kms254/Mustang-Dash-Test/docs/plans/2026-07-27-003-feat-telltale-driver-and-rail-decoupling-plan.md

---
title: Telltale Driver Chain and Rail Decoupling - Plan
type: feat
date: 2026-07-27
topic: telltale-driver-rail-decoupling
artifact_contract: ce-unified-plan/v1
artifact_readiness: implementation-ready
product_contract_source: ce-plan-bootstrap
execution: code
origin: docs/plans/2026-07-27-002-fix-board3-fab-ready-in-kicad-plan.md
---

# Telltale Driver Chain and Rail Decoupling - Plan

## Goal Capsule

- **Objective:** Replace Board3's Darlington telltale driver with a DMOS array, move the telltales to the PLCC-2 package the automotive industry uses for cluster indicators, re-derive the series resistors from the resulting electrical and photometric reality, and convert the rail bulk capacitance from through-hole to SMD sited at the loads that need it.
- **Continuity:** Units continue the fab-ready plan's numbering at **U10**; requirement IDs continue at **R18**. That plan closed at U9 with the board fab-ready (36 DRC violations, NEW = 0 against the 41-violation import baseline, 0 airwires).
- **Product authority:** Kevin owns the design decisions. This document owns sequencing and the completion bar.
- **Execution profile:** Real design work on a board already declared fab-ready. Every unit must leave it fab-ready.
- **Delivery split (decided 2026-07-27):** U10-U12 are a self-contained, shippable increment. **U13-U14 are GATED** and must not be started until their blocking input arrives.
- **Stop conditions:** Stop and report if DRC rises above the 41-violation import baseline; if a part cannot be sourced with complete LCSC metadata; if the PLCC-2 pitch does not fit; or if a change would alter circuit intent rather than implementation.

---

## Product Contract

### Summary

Board3's eight telltales are driven by a ULN2803A Darlington array whose ~0.8 V saturation drop consumes up to 44% of the available headroom on the high-V<sub>f</sub> colours, holding the blue telltale to 5 mA. Replacing it with a pin-compatible DMOS array drops that to ~5 mV and unlocks the brightness the design was aiming for. Once the driver changes, the series resistors must be re-derived anyway — which makes it the right moment to move the LEDs from 0805 to PLCC-2, the package automotive clusters use because it couples into an icon mask or light pipe instead of producing a hot spot.

Separately, the rail bulk is six 8 mm through-hole cans. Four sit on +5V clustered at the board's east end; two put 440 µF on the 3V3 buck output. They force a through-hole assembly step on an otherwise all-SMT board, and their placement serves only one of three panels.

### Problem Frame

**The driver wastes the headroom the high-V<sub>f</sub> telltales need.** Measured from the parts themselves:

| LED | Colour | V<sub>f</sub> | R now | I now (ULN2803A, ~0.8 V) |
|---|---|---|---|---|
| LED1/2 | green NCD0805G1 | 2.5 V | 390 Ω | 4.4 mA |
| LED3 | white KT-0805W | 2.6 V | 300 Ω | 5.3 mA |
| LED4 | blue XL-2012UBC | 3.2 V | 200 Ω | 5.0 mA |
| LED5 | orange XL-2012UOC | 2.3 V | 470 Ω | 4.0 mA |
| LED6/7 | red NCD0805R1 | 1.6 V | 270 Ω | 9.6 mA |
| LED8 | yellow KT-0805Y | 1.8 V | 300 Ω | 8.0 mA |

On the blue telltale the Darlington takes 0.8 V of the 1.8 V that remains after V<sub>f</sub>. A Darlington's drop also never falls below ~0.7 V and varies with current and temperature, so brightness tracks part spread rather than design intent.

**A second, quieter problem:** the ULN2803A's inputs are current-driven through internal 2.7 kΩ base resistors and are specified against 5 V logic. The H755 drives them at 3.3 V. It works, but with reduced margin — and it is not a condition anyone chose.

**The telltale package is wrong for the job.** 0805 LEDs are small, narrow emitters. Cluster telltales sit behind icon masks or light pipes, which is why PLCC-2 (Osram TOPLED and equivalents) is the industry package: a large emitting surface, ~120° beam, 30-50 mA capability, and an AEC-Q102 inventory that does not exist for these generic 0805 parts.

**The bulk capacitance is in the wrong package and the wrong place.** Six `ERS1EM221F12OT` (220 µF 25 V, THT, LCSC C160162): C1/C12/C13/C14 on +5V at x=260-269, plus C2 and C16 on +3V3. Each FPC already carries a local 10 µF ceramic (C30/C31/C29), and the buck has its input cap (C51). So the 880 µF is additional, is the rail's entire electrolytic budget, and sits at one end — 18 mm from FPC3, 111 mm from FPC2, 210 mm from FPC1. If PWM'd backlight droop justifies it at FPC3, FPC1 and FPC2 are under-provisioned by two orders of magnitude. If it does not, FPC3 does not need it either. Both cannot be true.

### Requirements

**Driver**

- R18. `U10` is a DMOS/MOSFET array whose on-state drop at telltale currents is under 50 mV, replacing the ULN2803A Darlington.
- R19. The replacement is pin-compatible with the existing SOIC-18-300mil land pattern, so the swap changes parts and not layout.
- R20. The replacement's input thresholds are specified for 3.3 V logic.

**Telltales**

- R21. All eight telltales use a PLCC-2 package.
- R22. Parts are AEC-Q102 automotive grade **where that colour is stocked at LCSC**, commercial grade otherwise, with the grade recorded per part.
- R23. The LED row's existing pitch accommodates the larger package without moving neighbouring parts.

**Brightness**

- R24. Series resistors are derived from each chosen LED's V<sub>f</sub> and luminous intensity so the eight telltales are matched in **perceived** brightness, not in current.
- R25. Each telltale runs at the highest current the chosen part and driver allow within their continuous ratings, since global dimming is done in firmware by PWM.

**Bulk capacitance** *(gated — see Scope Boundaries)*

- R26. Rail bulk capacitance is SMD, eliminating the through-hole assembly step.
- R27. Bulk is sited at each FPC's backlight supply pins (17/18 and 19/20), not clustered at one end of the board.
- R28. Total +5V bulk is sized from the panel's actual backlight current, and the resulting USB-C inrush through the U5/U6 ideal-diode ORing is stated.
- R29. The +3V3 bulk is reconciled against the TPS563201's maximum output capacitance for reliable start-up.

**Sourcing and provenance**

- R30. Every part added or changed carries the full metadata set the existing parts carry: `Supplier Part`, `Manufacturer Part`, `Manufacturer`, `JLCPCB Part Class`, `Datasheet`, `LCSC Part Name`.
- R31. Every new R/C/IC carries its value or model number in silkscreen on its own footprint body (standing project rule).
- R32. The board stays fab-ready at every unit boundary: DRC no worse than the 41-violation import baseline, zero airwires, no via inside an SMD pad.

### Scope Boundaries

- **Gated, not deferred: U13 and U14.** The bulk work is fully specified here but must not start until the Riverdi RVT70HSBNWN00 backlight current is known. Riverdi does not publish it in any indexed page; the datasheet PDF or a bench measurement is the unblocking input.
- No 6-layer restack. The reviewer's Top/GND/GND/5V proposal is directionally right about return-path integrity and infeasible on four layers — 2,072 mm of routing currently lives on the three non-top layers and would have to fit on a top layer already carrying 3,308 mm. That is a respin decision with its own plan.
- No inner-plane routing rework. Inner1 carries 934 mm of signal and Inner2 656 mm; that is the board's architecture, not a defect this plan fixes.
- No reopening of U6's walked-back crystal and QSPI work.
- No change to telltale colour assignment or count — eight positions, six colours, as built.
- Firmware is untouched. PWM dimming already exists and is how brightness is trimmed at runtime.

### Dependencies and Assumptions

- KiCad 10.0.5; `kicad-cli` and `pcbnew` reached through `tools/kicad_env.py`.
- Design rules come from `tools/kicad_rules.json`, never the board's `.kicad_pro` (KTD2 of the origin plan). The project file now carries a synced copy of those rules.
- **Update PCB from Schematic is GUI-only and Kevin-run**, with "Re-link footprints to schematic symbols based on their reference designators" ticked. It reads eeschema's cached copy, not the file — restart KiCad after any out-of-editor schematic edit or the sync silently reports no changes.
- Board3 as it stands: 36 DRC violations, NEW = 0 over the 41-violation import baseline, 0 airwires, 145 distinct references, CPL 141 rows, BOM 51 lines all sourced.
- `tools/kicad_fab.py` builds the JLC BOM from the `Supplier Part` field. A part added without it does not warn — it silently drops out of the BOM. This is why R30 is a build dependency rather than a preference.
- Assumed: the LED row's pitch accommodates PLCC-2. **U11 measures this first and stops if it does not.**

### Open Questions

**Blocking for U13-U14 only**

- Riverdi RVT70HSBNWN00 backlight LED current at full brightness, and whether the module's backlight driver takes PWM on its own dim pin. If it does, its input capacitance smooths the 5 V draw and the bulk requirement collapses.
- ~~The TPS563201's maximum output capacitance for reliable soft-start, against the present 440 µF.~~ **Answered 2026-07-28**, from the datasheet, while researching U15 of the origin plan. TI publishes **no absolute maximum** C<sub>out</sub> for this part. What it publishes is a *recommended range*: SLVSD90B Table 7-2's 3.3 V row gives C8+C9 = **20 to 68 µF**, restated in §7.2.2.2 as "Recommended values range from 20 µF to 68 µF". `C48`+`C49` = 44 µF sits mid-window; the 440 µF on `C2`/`C16` is ~6.5× the top of it.

  The binding constraint is not soft-start but **D-CAP2 loop stability, and it is two-sided** — SLVAF11 gives both an upper and a lower limit on C<sub>out</sub>, because crossover must stay above the internal ripple-injection zero for a −20 dB/dec crossing and below f<sub>sw</sub>/3. More bulk lowers crossover, and SLVA905 Table 4 measures phase margin *falling* when bandwidth drops below that zero. So "more capacitance is safer" is false for this topology. The catch: evaluating SLVAF11's limit needs the device's A<sub>cp</sub> and ω<sub>RI</sub> constants, which TI publishes for three other parts and **not** for the TPS563201 — so the computed bound is unavailable and Table 7-2's window is the authority.

  That leaves U13/U14 a better-posed question than "what is the maximum": **how much of the 440 µF the loop actually sees.** The +3V3 rail has no pour on any layer — 514.7 mm of 0.254 mm top-layer trace across 195 segments serving 74 pads — so distant bulk is decoupled from the control loop by real series resistance. `C2` measures 260.98 mm of routed path from `L2` pad 2, roughly 0.5 Ω at 1 oz copper; that is not a capacitor the loop can see. Bulk sited *close* to the buck output would be. U14's relocation to the FPC pins therefore wants a per-site path-length figure rather than a lump total, and it is moving bulk **nearer** the regulator that carries loop risk, not leaving it far away.

  Sources: SLVSD90B (Dec 2015, rev Sept 2024) Table 7-2 and §7.2.2.2; SLVAF11 §3.1 Eq 11 and 15; SLVA905 §2.2 Table 4. Path lengths measured from the board file. This resolves the C<sub>out</sub> half of the U13/U14 gate only — the backlight-current blocker above still stands, so the units stay gated.

**Resolvable inside U11-U12**

- ~~Which of the six colours are stocked at LCSC in AEC-Q102 PLCC-2, and what each one's V<sub>f</sub> and mcd-at-test-current are.~~ **Answered 2026-07-28** — the part set and its figures are KTD13. Two results worth stating apart from the table:

  **No colour is stocked in AEC-Q102 in this package**, so R22's conditional resolves to commercial grade across all eight positions. Caveat on how strong that negative is: LCSC does not expose AEC-Q102 as a filterable attribute — qualification lives in free text or only in the datasheet — so this is a negative from a weak search surface, the same shape as `docs/solutions/developer-experience/search-a-package-by-both-its-jedec-and-metric-names.md`. Enough to proceed on; not enough to call the catalogue exhausted.

  **The white part publishes no luminous intensity at all** — LCSC's `Luminous Intensity` for `C516299` is `-`, with a 6500 K colour temperature in its place. That is a real open input to U12, not a lookup that was skipped.

**New, blocking for U12 only**

- ~~White (`C516299`) has no published mcd, so it cannot be put on the same intensity axis as the other five from catalogue data.~~ **Answered 2026-07-28, by the second of the three listed routes** (the datasheet specifies flux, not intensity — there is no mcd bin table to read). From the manufacturer datasheet (SPEC NO B-17-A-1257, REV A/3, 2019-06-17, via LCSC):

  | CCT row | Φ min | Φ typ | conditions |
  |---|---|---|---|
  | 6500 K *(our 6000–7000 K variant)* | 7.5 lm | 8.5 lm | I<sub>F</sub> = 20 mA, tolerance ±10% |

  Also: V<sub>f</sub> 2.6–3.2 V at 20 mA, viewing angle 120°, Ra ≥ 80, SDCM ≤ 3.

  **Conversion to the row's axis:** a 120° part is Lambertian by definition (half-intensity at 60° *is* the cosine pattern), so I₀ = Φ/π: **typ ≈ 2 700 mcd, min ≈ 2 390 mcd**. Sanity: 8.5 lm ÷ (20 mA × ~3.0 V) ≈ 142 lm/W — right for a modern mid-grade white, so the conversion hides no error. The white is therefore the **brightest** position on the row's axis (green 1 300, orange ~1 800 loose, blue 350, red 270, yellow 210 mcd) — U12's matching target is set by the dim end, and the white takes a large resistor, not a guess. Use the **min** figure for worst-case matching; the ±10% flux tolerance and the Lambertian idealisation are the stated error bars.

---

## Planning Contract

Product Contract authored here (`ce-plan-bootstrap`) from the design review discussion of 2026-07-27; the origin plan supplied board state and the verification bar, not these requirements. **Product Contract preservation:** origin plan unchanged — this is a successor, not an edit.

### Key Technical Decisions

**KTD7. The driver is `TBD62083AFWG` (LCSC C165895, SOIC-18-300mil).** R<sub>DS(on)</sub> 325 mΩ, 8 channels, 2.5-30 V input, 2503 in stock. At 15 mA per channel the drop is **4.9 mV** against the Darlington's ~800 mV, and its input thresholds are specified for 3 V logic. It is the industry drop-in for the ULN2803A and matches U10's existing `SOIC-18_L11.6-W7.5-H2.7-LS10.3-P1.27` land pattern, so the board change is a part swap. `C108880` is the same die in SOP-18-300mil at roughly half the price if that land pattern turns out to suit better.

**KTD8. The LED package changes before the resistors are calculated, not after.** Both inputs to the resistor derivation — V<sub>f</sub> and mcd — are properties of the LED. Calculating resistors for the 0805s and then swapping the package throws the calculation away. U11 therefore precedes U12, and U12 consumes U11's chosen parts.

**KTD9 [superseded 2026-07-29 — the perceived-brightness principle survives as the calibration table's seed math; the resistor mechanism died with U12's supersession, see plan 2026-07-28-001 KTD17]. Resistors are derived for equal PERCEIVED brightness, not equal current.** The eye's photopic response peaks near 555 nm, so equal current across six colours produces visibly unequal telltales. The derivation is: for each part, read luminous intensity at its test current, pick a target perceived output achievable by every colour within its continuous rating, then solve `R = (5 − V_f − I·R_DS(on)) / I` per colour. Equal-current is the starting point and the wrong answer.

**KTD10. Mixed-grade BOM, tracked per part.** AEC-Q102 where a colour is stocked in it, commercial otherwise. This maximises availability without silently downgrading the whole row, and the grade is recorded per part so a future production run can close the gaps deliberately.

**KTD11. Every unit ends fab-ready, and "DRC clean" is not the bar.** U6's regression is the standing lesson: six vias buried inside the flash's SMD pads passed DRC and passed a length/via/layer measurement, because via-in-pad is neither. Each unit's verification therefore includes the pad audit and a `kicad_measure --against` diff proving only the intended nets moved.

**KTD12. The schematic-to-board loop has a human in it.** Each unit that changes parts follows: agent edits the schematic as text → **Kevin runs Update PCB from Schematic in the GUI** → agent places, routes, verifies. This is not a limitation to engineer around; it is the one step with no CLI equivalent. Units are shaped so each needs exactly one crossing of it.

**KTD13. The telltale row is HONGLITRONIC HL-A at 20 mA and 120°, except orange, which has no HL-A part and breaks the series deliberately.** Selected and verified against LCSC on 2026-07-28; all six are `SMD3528-2P`, all Extended library, all commercial grade (see Open Questions on AEC-Q102).

| Position | Colour | LCSC | MPN | V<sub>f</sub> | mcd @ 20 mA | Lens | Stock |
|---|---|---|---|---|---|---|---|
| LED1, LED2 | emerald green | `C516142` | HL-A-3528U51GC-S1-13HL | 3.4 V | 1300 | water clear | 65,431 |
| LED3 | white 6500 K | `C516299` | HL-A-3528H343W-S1-13HL-HR3 | 3.2 V | ≈2 700 (from 8.5 lm typ, Lambertian; min ≈2 390 — see Open Questions) | frosted yellow | 100,134 |
| LED4 | blue | `C516143` | HL-A-3528H203BC-S1-13HL | 3.4 V | 350 | water clear | 21,061 |
| LED5 | orange | `C5246349` | HVO-3528CPXA | 2.2 V | 1800 | white lens | 2,000 |
| LED6, LED7 | red | `C516141` | HL-A-3528S35FC-S1-13HL | 2.4 V | 270 | water clear | 26,687 |
| LED8 | yellow | `C516140` | HL-A-3528S31YC-S1-13HL | 2.4 V | 210 | water clear | 24,142 |

Holding one vendor series at one test current and one beam angle is what makes these mcd figures comparable at all — `docs/solutions/conventions/luminous-intensity-is-not-comparable-across-parts.md` is the reasoning, and it is load-bearing for U12.

**Orange is the exception and it is not a slip.** There is no HL-A 3528 orange at LCSC, so the choices were HVO-3528CPXA (orange, 1.8 cd, white lens) or HVA-3528CPXA (`C5246348`, amber, 560 mcd/1.8 cd). HVO wins on being the colour the board already calls for rather than a substitution, and on already carrying a vendor CAD model. The costs are real and should be visible rather than discovered later: it is a different series, so its figure is only loosely comparable to the other five; it has a **white diffusing lens** where the rest are water clear, which changes apparent colour and on-axis intensity independently of the number; stock is 2,000 against 21k-100k for the HL-A parts, the thinnest line in the row; and at $0.12 it is roughly 6× the others. If the orange telltale later needs re-sourcing, this is the position to expect it at.

**The blue is why a 3D model was hand-derived.** Everlight's `67-21/BHC-FQ1R2F/2T` (`C264601`) was the blue with a ready CAD model, quoted `72~180 mcd` — a 2.5× bin spread inside one part number, wider than the matching precision U12 is chasing. `C516143`'s single 350 mcd figure is worth more than a free STEP file, so the model was derived by recolouring a sibling HL-A body and the row stayed in series. `C264601`, `HVT-3528CPX` (`C5246350`, green) and `HVY-3528CPX` (`C2843418`, yellow) are the candidates this decision retired.

### High-Level Technical Design

```mermaid
flowchart TB
  subgraph SHIP["Shippable increment"]
    U10["U10 Driver swap<br/>ULN2803A -> TBD62083AFWG"]
    U11["U11 Telltales to PLCC-2<br/>8 positions, 6 colours"]
    U12["U12 Resistors re-derived<br/>perceived-brightness matched"]
  end
  subgraph GATED["GATED on the backlight spec"]
    U13["U13 Bulk THT -> SMD"]
    U14["U14 Bulk relocated to<br/>FPC pins 17/18 + 19/20"]
  end
  BLOCK{{"Riverdi backlight current<br/>+ TPS563201 max Cout"}}

  U10 --> U12
  U11 --> U12
  U12 --> DONE["Fab package regenerated"]
  BLOCK -.unblocks.-> U13
  U13 --> U14
  U14 --> DONE
```

The dependency that matters is U10 **and** U11 both feeding U12: the resistor value for each telltale depends on the driver's drop and on that LED's V<sub>f</sub> and mcd. U10 and U11 are independent of each other and can be authored in either order, but both must land before U12's arithmetic is real.

Per-unit, the loop is the same shape:

```mermaid
sequenceDiagram
  participant A as Agent
  participant K as Kevin (GUI)
  participant B as Board
  A->>A: edit .kicad_sch as text, verify by netlist export
  A->>K: hand off for Update PCB from Schematic
  K->>B: sync (re-link footprints ticked)
  A->>B: place, route, refill under real rules
  A->>A: DRC delta, airwires, pad audit, net diff
```

---

## Implementation Units

| U-ID | Title | Key files | Depends on |
|---|---|---|---|
| U10 | Driver swap to TBD62083AFWG | `kicad/board3/*.kicad_sch`, `*.kicad_pcb` | — |
| U11 | Telltales to PLCC-2 | `kicad/board3/*.kicad_sch`, `*.pretty/`, `*.kicad_pcb` | — |
| U12 | Resistors re-derived | `kicad/board3/*.kicad_sch`, `*.kicad_pcb` | U10, U11 |
| U13 | Bulk THT to SMD **(gated)** | `kicad/board3/*.kicad_sch`, `*.pretty/` | backlight spec |
| U14 | Bulk relocated to FPC pins **(gated)** | `kicad/board3/*.kicad_pcb` | U13 |

### U10. Swap the Darlington array for a DMOS array

**Goal:** Get the ~0.8 V driver drop out of the telltale chain.

**Requirements:** R18, R19, R20, R30, R31.

**Dependencies:** None.

**Files:** `kicad/board3/ProPrj_New Project_2026-07-15_23-14-34_2026-07-27.kicad_sch`, `kicad/board3/ProPrj_New Project_2026-07-15_23-14-34_2026-07-27.kicad_pcb`

**Approach:** Change U10's part from `ULN2803A` (C181731) to `TBD62083AFWG` (C165895) by editing the symbol's properties in place — value, footprint if the land pattern differs, `Supplier Part`, `Manufacturer Part`, `Manufacturer`, `JLCPCB Part Class`, `Datasheet`, `LCSC Part Name`. Confirm before editing that the two parts agree on all 18 pins: inputs 1-8, GND 9, COM 10, outputs 11-18, and that the replacement carries the output clamp diodes to COM that the flyback path relies on. If the existing SOIC-18 land pattern matches, the PCB change is nil and no re-placement is needed.

**Execution note:** Verify the pinout against the datasheet before touching the schematic. A "pin-compatible" part that is not is the failure mode here, and it is silent until assembly.

**Patterns to follow:** The property set on any existing sourced part; `tools/kicad_lcsc.py` documents which field names this project reads.

**Test scenarios:**
- Covers R18. Netlist export shows U10's eight input nets and eight output nets unchanged, node-for-node, against the pre-edit netlist.
- Covers R19. The footprint property is unchanged, or if changed, the new land pattern is verified against the part's datasheet dimensions.
- Covers R30. `python tools/kicad_fab.py kicad/board3/ --out fab/` reports the same "51 sourced, 0 without LCSC or MPN" — the new part appears with its LCSC code, not blank.
- Covers R32. DRC delta is zero and airwires stay at 0.
- ERC delta is zero or fully attributable to the part change.

**Verification:** U10 carries the DMOS part with complete metadata, the netlist is unchanged, and the board is untouched or re-verified.

### U11. Move the telltales to PLCC-2

**Goal:** Put the eight telltales in the package cluster indicators actually use.

**Requirements:** R21, R22, R23, R30, R31.

**Dependencies:** None.

**Files:** `kicad/board3/ProPrj_New Project_2026-07-15_23-14-34_2026-07-27.kicad_sch`, `kicad/board3/ProPrj_New-easyedapro.pretty/`, `kicad/board3/ProPrj_New Project_2026-07-15_23-14-34_2026-07-27.kicad_pcb`

**Approach:** ~~**Measure the LED row pitch first.**~~ **Measured 2026-07-28. R23 passes, and the premise behind it was wrong.**

**The telltales are not a row.** They are two 2×2 clusters at opposite ends of a 250 × 50 mm board, 150 mm apart: LED1/3/5/7 at x = 65/75, LED2/4/6/8 at x = 225/235, all at y = 90 and 95, every part at rot −90. Pitch is **10.000 mm in X, 5.000 mm in Y**, identical in both clusters. Nothing in this unit depends on the row reading, but the plan asserted it and the board does not support it — later work should not inherit it.

Clearance is computed per adjacent pair as `pitch − halfA − halfB` from the authored courtyards and the real placement, because the six parts have different land patterns and the tightest pair is not the average one. The Y axis (5.000 mm pitch, parts at rot −90 so each package's long axis runs vertically) is the only one that is close:

| Pair | Colours | Σ half-courtyard | Gap |
|---|---|---|---|
| LED4 ↔ LED6 | blue + red | 4.750 mm | **0.250 mm** |
| LED3 ↔ LED7 | white + red | 4.543 mm | 0.457 mm |
| LED1 ↔ LED5 | green + orange | 4.200 mm | 0.800 mm |
| LED2 ↔ LED8 | green + yellow | 4.150 mm | 0.850 mm |
| all X pairs | — | 3.300 mm | 6.700 mm |

**R23 is satisfied — every gap is positive and no neighbour moves** — but the worst case falls from **1.300 mm today to 0.250 mm**, a 5× reduction concentrated on one pair. The blue is the driver: its land pattern is the widest of the six (5.100 mm courtyard against 4.100-4.685 for the rest). Treat y = 90-95 as spoken for from here on, and expect `courtyards_overlap` to be sensitive to any future nudge in that band.

These are **predicted** figures — the board still carries 0805 land patterns until the GUI sync, so they are computed from placement plus the authored courtyards, not read back from a synced board. Confirming them is part of the board half.

**The imported footprints have no courtyard at all, and that has to be fixed here.** All nine `JLCImport.pretty/` footprints carry only `F.Cu`, `F.SilkS` and `F.Fab` — JLCImport does not emit `F.CrtYd`. This is not cosmetic:

- `courtyards_overlap` is **25 of the board's 36 DRC violations**. Swapping in eight courtyard-less footprints makes that count *fall*, and not because the board improved — eight parts would simply stop being checked. A DRC delta computed across that swap would read as an improvement while measuring less than it did before. This is `docs/solutions/conventions/a-gate-that-cannot-pass-gets-waved-through.md` exactly.
- R23 is enforced by courtyard clearance. Without a courtyard there is nothing for DRC to enforce, and the 0.600 mm above is a number no tool will ever re-check.

So U11 authors `F.CrtYd` on the six footprints it uses, sized IPC-7351-style at 0.25 mm around the true occupied extent (pads dominate the long axis at ±1.95 mm, the silk body dominates the short axis at ±1.40 mm → 4.40 × 3.30 mm for the representative part; compute per part rather than assuming, since body length varies 3.2-3.5 mm across the set). The 0.600 mm figure above is the number this makes enforceable.

Part selection is closed — **KTD13 is the answer**, verified against LCSC on 2026-07-28, and its six parts are already imported into `JLCImport.kicad_sym` / `JLCImport.pretty/` with 3D models. What remains is applying them: swap each of LED1-8's `lib_id`, `Value`, `Footprint` and the full supplier field set, then hand off for the board sync.

**This unit splits at the GUI boundary, and the split is the point.** 0805 → PLCC-2 is a *footprint* change, which is the case `kicad/README.md` and KTD12 say genuinely needs Update PCB from Schematic — unlike U10's pure part swap onto an identical land pattern, which `fp.SetValue()` closed with no sync. So:

- **Schematic half (agent, autonomous):** symbol swap, metadata, retired-import cleanup, pitch measurement, and every check that reads the schematic — netlist, ERC, `kicad_lcsc.py check` and `duplicates`.
- **Board half (Kevin, GUI, then agent):** Update PCB from Schematic with re-link-by-reference ticked and KiCad restarted first, then placement, DRC delta, pad audit, renders and fab regeneration.

The intermediate state is a repo where the schematic specifies 3528 and the board still carries 0805 land patterns. That is legible and intentional, but it is **not fab-ready** — do not regenerate `fab/` from it, and say so on any PR that lands the schematic half alone.

**The symbol swap is polarity-unsafe and is not a field edit. Discovered 2026-07-28, and it stops the swap.**

Both sides of this swap use inconsistent anode/cathode conventions, so a symbol-for-symbol replacement silently reverse-biases some telltales.

The board today, read from pad nets:

| Anode on pad 1 | Anode on pad 2 |
|---|---|
| LED1, LED2, LED3, LED8 | LED4, LED5, LED6, LED7 |

This is not a defect — it is the faithful image of six source symbols that disagree with each other (`FC-2012UGK-520D5` and `whiteLEDSMD` put pin 1 = A at x +5.08; `XL-2012UBC`, `XL-2012UOC` and `FC-2012HRK-620D` put pin 1 = K/− at x −5.08; `17-21SUYC/TR8` puts pin 1 = + at x +5.08). The replacements disagree too, and differently: `HL-A-3528U51GC` is pin 1 = C at x −5.08, `HVO-3528CPXA` is pin 1 = K at x −5.08, but `HL-A-3528S35FC` is pin 1 = K at **x +5.08** — mirrored against its own siblings.

Two independent hazards, only one of which any gate catches:

- **Geometric.** Schematic wires attach at coordinates. When pin 1 moves from x +5.08 to x −5.08, the wire that met pin 1 now meets pin 2 and the nets swap. The netlist diff catches this.
- **Electrical.** Anode and cathode change pin number without changing net topology. The netlist still shows two nodes on the right nets, **ERC passes, DRC passes, the BOM is correct, and the telltale is fitted backwards.** Behind a low-side DMOS array a reversed LED simply never lights. Nothing in the verification contract sees it — this is KTD11's lesson in a new place.

So each position needs its anode pin landed on `/+5V` and its cathode on `/TT*_LED_K` individually, by choosing the symbol instance's mirror/rotation per LED — not by rewriting `lib_id` and the property block.

**Resolved 2026-07-28 (Kevin): normalise, and the geometry allows it.**

**KTD14. Every telltale is wired pad 1 = cathode, pad 2 = anode.** Three things make this cheap rather than the re-routing exercise it first looked like:

- **All six replacements already agree electrically.** Pin/pad 1 is the cathode on every one — `C`, `K` or `−` depending on how the vendor labelled it. The red `HL-A-3528S35FC` is *geometrically* mirrored (pad 1 at local x +1.35 where its five siblings put it at −1.35), but it is internally self-consistent, so it needs no special handling in net assignment. Only its physical approach side differs.
- **Only four positions move.** LED4/5/6/7 already carry the cathode on pad 1. LED1, LED2, LED3 and LED8 are the swap set.
- **No copper is in the way.** No track segment terminates on any of the sixteen telltale pads — checked against all 2,487 segments on the board, not a sample. There is nothing to rip up at the LED end, and the land pattern is changing anyway (0805 pads at ±1.10 to 3528 pads at ±1.35/1.49/1.55), so that copper is being remade regardless.

The alternative — preserving the board's existing per-position polarity — was rejected as a preference: it is the smaller diff but it carries an inconsistency that exists only because six imported symbols disagreed, and it leaves the next person to rediscover this the hard way.

**The board half was attempted in script and reverted. 2026-07-28.** Worth recording because it sharpens the "GUI-only" rule rather than just confirming it.

`pcbnew` *can* do a targeted footprint replacement — `FootprintLoad`, `board.Add`/`Remove`, `SetPosition`/`SetOrientationDegrees`, `pad.SetNet` and `board.FindNet` are all exposed and all work. The eight telltales were swapped, positions and orientations preserved, Value/Reference field layers carried over, and every pad assigned from the netlist (pad 1 = cathode, pad 2 = anode). The script ran clean. **The board it produced is worse, so it was reverted:**

| | baseline | after swap | after zone refill |
|---|---|---|---|
| `shorting_items` | 0 | 24 | **25** |
| `solder_mask_bridge` | 0 | 39 | 25 |
| `clearance` | 0 | 19 | 4 |
| `courtyards_overlap` | 25 | 26 | 26 |
| unconnected | 0 | 3 | 3 |
| **total** | **194** | 286 | 258 |

Refilling zones first (per `docs/solutions/developer-experience/refill-zones-before-measuring-a-headlessly-routed-board.md`) fixed most of the clearance and mask-bridge noise and **did not touch the shorts**, so the fill was not the cause.

**Second attempt, with placement search and re-routing. Also reverted, but it produced the recipe.** DRC went 194 → 286 → 258 → **231** across three passes. Still +37, so it did not ship; what it bought is a diagnosis specific enough to act on.

The earlier "all six zones are netless" reading was **wrong** — a text-parsing error, the third this session on this file. Read through `pcbnew`, the zones are healthy: `/GND` pours on Top, Bottom and Inner1 (all filled), a `/+5V` pour on Inner2, and two Inner2 keepout rule areas that are netless *by definition*. Nothing anomalous. Use `pcbnew` for board facts, never regex.

**The conflicts are ordinary and there are two kinds:**

1. **Stale stubs.** The old copper was routed to the old pad positions. Normalisation swapped pad 1 and pad 2, so a `/+5V` stub now lands on LED6's cathode and a `/TT7` stub on LED7's anode. 32 segments, all short.
2. **Bigger pads reaching foreign nets.** `/USB_DP` at LED3 (13 violations — the USB pair runs right past it), `/CS_R` at LED8, `/PD_R` at LED2 and LED6, `/GND` at LED8. Rerouting USB is forbidden by the origin plan's R37, so the telltales move, not the pair.

**A collision-free placement exists and is cheap.** Searching rotation × offset against every foreign-net shape on F.Cu (via `GetEffectiveShape(F_Cu).Collide`) finds zero-collision positions for all eight within 1.5 mm, keeping rot −90 throughout, so the icon grid survives:

| | LED1 | LED2 | LED3 | LED4 | LED5 | LED6 | LED7 | LED8 |
|---|---|---|---|---|---|---|---|---|
| Δx mm | 0 | −0.25 | −0.25 | 0 | 0 | −0.25 | 0 | **−1.50** |
| Δy mm | 0 | −0.25 | +0.25 | 0 | 0 | +0.50 | 0 | +0.50 |

Only LED8 moves visibly, and only to clear `/CS_R`.

**What actually blocks the scripted route, and it is topology not geometry: `/+5V` daisy-chains *through* the telltale pads.** `C30`'s supply path runs pad-to-pad through a telltale, so deleting a stale stub at an LED pad breaks the chain onward to `C30` — which is why `C30` pad 1 shows unconnected after an otherwise correct edit. A nearest-endpoint connector reconnects the near side and cannot know it has orphaned the far side; that also produced the 2 `tracks_crossing` against `/PD_R` and 3 `track_dangling`. Re-routing this area means re-establishing a chain, not drawing eight independent stubs, and that wants a real router or the GUI.

**Third attempt: a real autorouter, and it very nearly lands it.** `tools/kicad_route.py` (KiCadRoutingTools, cloned beside the repo) does what the hand-rolled connector could not — handed a board that is complete *except* the telltale pads, it re-establishes the `/+5V` chain through to `C30` and closes **14 airwires → 0**.

Reproduce with `tools/kicad_fit_telltales.py`, which swaps the footprints, deletes only the stubs that actually land on an old telltale pad, and solves placement:

```
python.exe tools/kicad_fit_telltales.py <out>.kicad_pcb noroute   # KiCad's interpreter
cp <board>.kicad_pro <out>.kicad_pro                              # router reads sibling rules
python.exe tools/kicad_route.py <out>.kicad_pcb --out <routed>.kicad_pcb
```

**Result: DRC 194 → 221 (+27), unconnected 0, crossings 0.** Twenty of the +27 are silkscreen (`silk_overlap` +11, `silk_over_copper` +9) — the 3528 silk is larger than the 0805 silk and the board already carried 150 such warnings. The electrical residue is **four**: one `shorting_items` (`/+5V` against `/TT6_LED_K`, the router's own feed passing its other pad), one `solder_mask_bridge`, one `hole_clearance`, one `track_dangling`.

**It is not committed, because one short is a hard fail.** Four calibration passes were run and 0.15 mm is the optimum — the numbers are worth keeping so nobody re-derives them:

| pad-to-foreign-copper margin | result |
|---|---|
| **0.15 mm** | **all 8 placed, DRC 221, 1 short** |
| 0.25 mm | LED3 unplaceable, DRC 382 |
| 0.40 mm | LED3 + LED8 unplaceable, DRC 382 |
| 0.15 mm, LED6 relaxed to 0.35 | DRC 354 |

Loosening is counter-productive: a larger margin pushes parts further from home, and the extra displacement costs more than the clearance buys.

**What is left is one trace.** Run the two commands above, then in the GUI delete and re-draw the single `/+5V` segment that passes LED6's cathode pad. That also clears the mask bridge, which is the same copper. Everything else — placement, polarity, the `/+5V` chain, zero airwires — is already correct in the generated board.

**The original shorts, for the record.** A representative one is `Items shorting two nets (nets /TT6_LED_K and /+5V)` — LED6's own two pads bridging. The 3528 land pattern puts 1.2 × 2.5 mm pads at ±1.35 mm, a 1.5 mm edge-to-edge gap, so they cannot bridge each other. Something else carrying copper across them must be doing it, and the likeliest candidate is the same anomaly noted below: **all six copper zones parse with no net**. Netless filled copper touching both pads shorts them by definition, and the smaller 0805 pads evidently sat clear of it where the 3528 pads do not.

So the conclusion is narrower and more useful than "the API cannot do it": **the API can place the footprints; the board is not ready to receive them until the netless-zone question is answered.** That is layout work with a real design question inside it, not a scripting gap. Do not re-attempt the scripted swap before the zones are understood — it will reproduce the same 25 shorts.

**Unresolved, and now load-bearing rather than a curiosity:** DRC reports **0 unconnected** on the current board, which does not square with sixteen pads carrying no track. All three large copper zones (`F.Cu`, `B.Cu`, `In1.Cu`) parse as netless, so what is satisfying connectivity there is not identified. It does not change this decision — nothing needs re-routing either way — but the ratsnest will show the truth the moment Update PCB from Schematic runs, and a surprise there should stop the unit rather than be routed around.

**Cross-reference:** the board-layout consequences of this working session were carried forward as **U16–U18 in plan 002** (`2026-07-27-002-fix-board3-fab-ready-in-kicad-plan.md`) — U2 pushed east for the crystal lane, the QSPI escape vias slid east, and `/CS_R`/`/PD_R` re-pinned and rerouted — which owns that stretch of the shared U-ID space (KTD8).

**Retire the superseded imports.** Three parts were imported during selection and lost: `67-21_BHC-FQ1R2F_2T` (`C264601`), `HVT-3528CPX` (`C5246350`), `HVY-3528CPX` (`C2843418`). Each carries a ~1.3-1.7 MB STEP plus a WRL. Remove their symbols, footprints and models rather than leaving three unreferenced parts a future reader has to disprove — git history keeps them if the decision is ever revisited.

**Execution note:** The pitch measurement gates the swap. Take it first and report the number even if it passes; R23 is satisfied by evidence, not by the absence of a complaint.

**Test scenarios:**
- Covers R23. Every adjacent pair has positive courtyard clearance, reported per pair rather than as a pass/fail: worst **0.250 mm** (LED4↔LED6, Y), best 6.700 mm (all X pairs). See the table above.
- Covers R23's enforceability. Each of the six footprints carries an `F.CrtYd` outline; a scan of `JLCImport.pretty/` finds no footprint in use without one. Without this the clearance above is unenforced and the board's `courtyards_overlap` count silently stops covering these parts.
- Covers R21/R22. Each of the eight positions carries a `SMD3528-2P` part; grade is recorded per part (all commercial — see Open Questions).
- Covers R30. All eight carry complete supplier metadata; `python tools/kicad_lcsc.py check` reports every placed part LCSC-mapped and modelled, and `duplicates` reports no one-code-several-values conflict.
- The eight LED nets keep their existing node sets — `kicad-cli sch export netlist` diffs to zero node changes. The swap changes parts, not connectivity.
- ERC delta is zero: the JLCImport symbols' pin types match the parts they replace.
- No reference to a retired part survives anywhere in `kicad/board3/` after cleanup.
- **Board half, post-sync (Kevin):** DRC delta zero, airwires 0, no via inside any new LED pad, renders refreshed.

**Verification:** Schematic half — eight 3528 telltales specified, pitch measured and reported, every part sourced, netlist and ERC unchanged, retired imports gone. Board half — synced, placed and fab-ready at the standing bar.

### U12. Re-derive the series resistors for matched perceived brightness

> **SUPERSEDED unfabbed, 2026-07-29** by the I2C revision
> ([2026-07-28-001](2026-07-28-001-feat-i2c-peripheral-consolidation-plan.md),
> KTD17): the TBD62083 and all eight series resistors left the board before
> any resistor was ever fitted; brightness matching became the firmware
> calibration table in `MustangDash/dash_calibration.h`, seeded from KTD13's
> photometry (this unit's own inputs — the measurement work was not wasted).
> The derivation below is retained as the record of the superseded approach.

**Goal:** Set each telltale's current so the row looks even at full brightness, with firmware PWM as the global dimmer.

**Requirements:** R24, R25, R30, R31.

**Dependencies:** U10, U11.

**Files:** `kicad/board3/ProPrj_New Project_2026-07-15_23-14-34_2026-07-27.kicad_sch`, `kicad/board3/ProPrj_New Project_2026-07-15_23-14-34_2026-07-27.kicad_pcb`

**Approach:** For each of the eight positions, solve `R = (5 − V_f − I·R_DS(on)) / I`, where `I` comes from equalising luminous intensity across colours rather than equalising current. Bound `I` by the lower of the LED's continuous rating and a sane derate; the driver is not the constraint (500 mA/channel, and eight channels at 15 mA dissipates under a milliwatt in total). Snap to E24 values available as LCSC Basic parts and record the resulting current and the deviation from target for each position.

Worth stating for review: at a uniform 15 mA the values would be green 160 Ω, white 160 Ω, blue 120 Ω, orange 180 Ω, red 220 Ω, yellow 220 Ω. **These are the equal-current answer and therefore the wrong one** — they are included only as the sanity check the real derivation should beat.

**Execution note:** Show the arithmetic in the commit. Someone will want to re-derive this when a colour goes out of stock, and the inputs (V<sub>f</sub>, mcd, test current) matter more than the answer.

**Test scenarios:**
- Covers R24. A table records, per position: part, V<sub>f</sub>, mcd at test current, chosen I, chosen R, resulting I, and relative perceived output — with the spread across the eight positions stated.
- Covers R25. No position exceeds its LED's continuous current rating; the margin is stated per position.
- Covers R30. Every changed resistor value resolves to an in-stock LCSC Basic part with complete metadata.
- Covers R32. DRC delta zero, airwires 0.
- Sum of telltale currents is within the driver's per-channel and package limits, stated as a number.

**Verification:** Eight resistors re-valued from measured part data, the derivation recorded, board fab-ready.

### U13. Convert rail bulk from through-hole to SMD — **GATED**

> **Do not start.** Blocked on the Riverdi RVT70HSBNWN00 backlight current and the TPS563201's maximum output capacitance. Starting this without those numbers means guessing at a rail whose IR-drop behaviour has already cost a bench night.

**Goal:** Remove the through-hole assembly step and size the bulk to the actual load.

**Requirements:** R26, R28, R29, R30, R31.

**Dependencies:** Backlight current spec; TPS563201 max C<sub>out</sub>.

**Files:** `kicad/board3/ProPrj_New Project_2026-07-15_23-14-34_2026-07-27.kicad_sch`, `kicad/board3/ProPrj_New-easyedapro.pretty/`

**Approach:** Size total +5V bulk from the backlight current and the PWM behaviour, then choose SMD parts. `189RV0019` (LCSC C7471881, 220 µF 35 V, D6.3 × 7.7 mm, **ESR 160 mΩ, 600 mA ripple**) is the leading candidate precisely because it publishes ESR and ripple; the cheaper 220 µF SMD parts rate 120-150 mA ripple, which matters if these absorb PWM pulses. Separately, reconcile the 440 µF on +3V3 (C2, C16) against the buck's stated maximum and reduce if it exceeds it.

**Test scenarios:**
- Covers R28. Total +5V bulk is stated with the calculation from backlight current, and the resulting inrush through the U5/U6 ideal diodes at USB-C attach is stated in amps.
- Covers R29. The +3V3 bulk is at or under the TPS563201's documented maximum, with the figure cited.
- Covers R26. No through-hole capacitor remains on either rail; the CPL shows the parts as SMD.
- Covers R30/R32. All parts sourced; DRC delta zero; airwires 0.

**Verification:** Rail bulk is SMD, sized from a cited number rather than inherited, and the inrush consequence is written down.

### U14. Relocate bulk to the FPC backlight pins — **GATED**

> **Do not start.** Depends on U13.

**Goal:** Put the bulk where the current is drawn.

**Requirements:** R27, R31, R32.

**Dependencies:** U13.

**Files:** `kicad/board3/ProPrj_New Project_2026-07-15_23-14-34_2026-07-27.kicad_pcb`

**Approach:** Place bulk adjacent to each FPC's backlight supply pins — 17/18 (BLVDD) and 19/20 (BLGND) — on FPC1, FPC2 and FPC3, rather than the present cluster at x=260-269. Present distances to the nearest +5V bulk are FPC1 210 mm, FPC2 111 mm, FPC3 18 mm; the target is comparable and short for all three. Route the connections short and wide, and take the ground return to the pour rather than a thin trace — the shared-ground IR-drop learning in `docs/solutions/` is exactly this failure.

**Test scenarios:**
- Covers R27. Distance from each FPC's backlight pins to its nearest bulk capacitor is stated for all three and is within the target set in U13.
- Covers R32. DRC delta zero, airwires 0, and the pad audit shows no via inside an SMD pad.
- `kicad_measure --against` shows only the intended nets changed.
- Each FPC's backlight ground return reaches the pour with at least two vias.

**Verification:** All three panels have local bulk, measured; board fab-ready.

---

## Verification Contract

| Gate | Command | Applies to |
|---|---|---|
| Toolchain resolves | `python tools/kicad_env.py` | any |
| Schematic connectivity | `kicad-cli sch export netlist` — the netlist KiCad syncs from | U10-U13 |
| DRC with baseline attribution | `python tools/kicad_verify.py <board> --baseline <import>` | U10-U14 |
| Net-level change proof | `python tools/kicad_measure.py <board> --against <before>` | U10-U14 |
| Via-in-pad audit | pad-vs-via scan across all four layers | U11, U12, U14 |
| Sourcing and fab outputs | `python tools/kicad_fab.py kicad/board3/ --out fab/` | U10-U14 |
| Automated review | `python tools/kicad_review.py kicad/board3/` | U11, U14 |

The DRC bar is a delta, not an absolute: no new violations over the 41-violation import baseline. The review harness's calibration must report `CALIBRATED` — if it reports `STALE`, its fixture needs repointing before its findings mean anything.

## Definition of Done

- U10-U12 complete: the DMOS driver is in place, eight PLCC-2 telltales are fitted, and the series resistors are derived from measured V<sub>f</sub> and mcd for matched perceived brightness.
- Every added or changed part carries complete LCSC metadata and a silkscreened value on its own footprint body.
- The board is fab-ready at the same bar the origin plan set: DRC no worse than the 41-violation import baseline, zero airwires, no via inside an SMD pad.
- `fab/` is regenerated so the BOM, CPL and gerbers reflect the new parts.
- U13 and U14 remain explicitly gated, with their blocking inputs named, until the backlight current and the buck's maximum output capacitance are known.
