kms254/Mustang-Dash-Test/docs/plans/2026-07-09-002-feat-dash-layout-plan.md

---
title: Dash Layout - Plan
type: feat
date: 2026-07-09
topic: dash-layout
artifact_contract: ce-unified-plan/v1
artifact_readiness: implementation-ready
product_contract_source: ce-brainstorm
execution: code
deepened: 2026-07-09
---

# Dash Layout - Plan

## Goal Capsule

- **Objective:** Recreate the Claude Design "EVE Triple Dash" center 7" screen on the RVT70H at native 1024×600 — TRACK and STREET modes, alarm takeover, telltales, odometer — driven by a built-in simulator with serial override until CAN lands. As part of the round (user-directed): migrate the boot splash's assets from RAM_G to the panel's onboard QSPI flash, so RAM_G belongs entirely to the dash fonts and the splash crossfades directly into the dash.
- **Product authority:** The design handoff vendored into the repo (README spec, interactive HTML mock, two reference renders — vendored by U1 into `assets/dash-design/`), plus the decisions in this contract.
- **Open blockers:** None.

---

## Product Contract

### Summary

Build the production dash for the center 7" panel from the design handoff: two switchable views (TRACK: shift lights, GPS-speed hero, RPM bar, lap/delta column; STREET: dual sweep gauges with non-linear speedo, telltale dots, odometer) plus a full-screen flashing alarm takeover. A firmware simulator feeds every channel until CAN integration, controllable over serial and via a `/dash` Claude command. Typography is real: Saira Condensed and Chakra Petch converted to EVE bitmap fonts. The boot splash transitions into the dash; the pony screen retires.

### Key Decisions

- **Native 1024×600, proportional rescale.** The design doc targets 800×480; the RVT70H is 1024×600. All layout scales proportionally (the design doc itself directs "treat all layout as proportional percentages of the panel"). Acceptance against the reference renders is therefore proportional — geometry, colors, and hierarchy must match; no pixel-diff.
- **Simulator behind the future CAN's data interface.** Live channels (rpm, speed, temps, pressures, laps, PMU states…) flow through one data interface; the simulator implements it now, the CAN decoders (Coyote Gen 4 control pack, 2× ECUMaster PMU16, RaceCapture) implement it later without touching render code.
- **Serial override is the bench control surface.** A line-based serial protocol forces values, states, mode, and alarms (`set rpm 3500`, `mode track`, `alarm oilp`, `odo set 24318`); a repo `/dash` Claude command wraps it. Mode switching arrives via this path now and via a CAN message later — same instant-swap behavior either way.
- **Full Phase 1 including odometer persistence.** EEPROM-backed odometer/trip ships now, fed by simulated distance; `odo set` corrects the accumulated fiction when real data arrives.
- **Custom EVE fonts via our own converter.** Saira Condensed (numerals, multiple sizes up to the hero) and Chakra Petch (labels) convert to EVE bitmap fonts with a Pillow-based tool in `tools/` — no EVE Asset Builder. This is the round's main new tooling; ROM fonts are not an acceptable fallback for the hero numerals per the spec's "high-fidelity, final" typography.
- **All rendering is procedural.** The design uses no raster assets — arcs, pills, LEDs, and lattices are display-list geometry. RAM_G is spent on fonts, not bitmaps.

### Requirements

**Design package and fidelity**

- R1. The design handoff (README spec, `Eve Race Dash.dc.html` + `support.js` interactive mock, both reference renders) is vendored into the repo so the dash can be built and verified without the external Downloads folder.
- R2. Layout, colors, typography, spacing, and gauge geometry follow the design doc's tokens and geometry spec, proportionally scaled to 1024×600; the two reference renders are the visual acceptance targets.

**TRACK mode**

- R3. Shift lights: 15 LEDs across the top, linear 0–8000 RPM (533 RPM each); LEDs 1–10 green, 11–13 amber, 14–15 red; above 7600 RPM all 15 flash red at ~8 Hz.
- R4. GPS SPEED hero numeral (left two-thirds) with label and MPH unit, per the spec's type hierarchy.
- R5. RPM linear bar with live value (white below 7100, amber 7100–7600, red above 7600), gold fill turning red above 7600, redline marker at 96%, and 0/2/4/6/8 scale marks.
- R6. Right column: LAP TIME readout and DELTA value with center-zero delta bar — green filling left when ahead of best, red filling right when behind, ±1.0 s full scale.

**STREET mode**

- R7. Dual sweep gauges sharing the spec's 240° gauge geometry: dominant speedometer (0–200 MPH, non-linear — 0–140 occupies 82.35% of sweep, 140–200 compressed, high labels smaller/dimmer) and smaller tachometer (0–8000, static red-zone arc 7600–8000, fill red above 7600), each with needle, gold value arc, and hub readout.
- R8. Warning telltale dots (FUEL / OIL / ECT / VOLTS) in a dead-front row: near-invisible when off, filled + glowing + colored label when triggered, per the spec's thresholds.
- R9. Odometer at bottom center (label, value, MI).

**Alarm takeover (both modes)**

- R10. A full-screen overlay flashing between bright-red and near-black at ~2.8 Hz preempts everything while any alarm condition holds: OIL PRESSURE < 29 psi, OIL TEMP > 248°F, COOLANT > 217°F, with priority oil pressure > oil temp > coolant; content shows WARNING header, alarm title, live value, and limit line per the spec.
- R11. Missing data never renders a stale alarm; absent channels display `--`.

**Data, simulator, and serial control**

- R12. All live channels flow through one data interface; the built-in simulator implements it with realistic motion (RPM/speed through gears using the vehicle constants, temps warming, lap timer running) so every visual state — thresholds, flash, alarms, delta — is reachable on the bench.
- R13. A line-based serial protocol overrides any channel or state: at minimum set <channel> <value>, mode track|street, alarm <which|off>, odo set <miles>, and a way to resume pure simulation.
- R14. A `/dash` Claude command in the repo wraps the serial protocol (e.g. `/dash set-rpm 3500`), following the `/reboot-dash` skill pattern.
- R15. Gauges update smoothly at ≥ 30 fps; mode switches are instant.

**Persistence and boot flow**

- R16. Odometer and trip persist across power cycles (EEPROM), integrated from (currently simulated) distance; `odo set` reseeds the stored value.
- R17. The boot splash crossfades into the dash, which becomes the standing display; the pony screen is removed from the boot flow. Existing serial boot diagnostics and the splash's visual behavior are unchanged (its asset storage moves to panel flash — see KTD11).

### Key Flows

- F1. Normal boot
  - **Trigger:** Power-up (car or bench).
  - **Steps:** Splash plays as today (from panel flash); it crossfades into the dash in its default mode; simulator starts feeding channels; render loop runs continuously.
  - **Outcome:** Live dash within roughly today's splash-to-screen timing of power-on. **Covers R12, R15, R17.**
- F2. Mode switch
  - **Trigger:** `mode street` / `mode track` over serial (later: CAN message).
  - **Steps:** Next frame renders the other view; no animation, no state loss (odometer, lap data, alarm state carry over).
  - **Outcome:** Instant swap, per spec. **Covers R13, R15.**
- F3. Alarm lifecycle
  - **Trigger:** Any alarm channel crosses its threshold (sim, override, or later CAN).
  - **Steps:** Takeover overlay preempts the active mode, flashing at ~2.8 Hz, showing the highest-priority active alarm with its live value; when the condition clears (or `alarm off`), the previous mode view returns.
  - **Outcome:** Un-missable alarm; no stale alarms. **Covers R10, R11.**
- F4. Bench control via Claude
  - **Trigger:** `/dash set-rpm 7700` in Claude Code.
  - **Steps:** Skill sends the line over the serial port; firmware acks; shift lights flash red on the panel.
  - **Outcome:** Every threshold and state testable from the conversation. **Covers R13, R14.**

### Acceptance Examples

- AE1. **Covers R3.** Given RPM is forced to 7700, when TRACK mode is shown, then all 15 shift LEDs flash red at ~8 Hz and the RPM value and bar render red.
- AE2. **Covers R5.** Given RPM is 7300, then the RPM value renders amber and the bar fill remains gold (amber pre-warning band is 7100–7600).
- AE3. **Covers R6.** Given the sim lap is 0.4 s ahead of best, then the delta reads green negative and the delta bar fills left of center at 40% of the half-width (±1.0 s equals full half-width).
- AE4. **Covers R7.** Given speed is 160 MPH, then the speedo needle sits in the compressed 140–200 region and the 160 label renders smaller and dimmer than the 0–140 labels.
- AE5. **Covers R8.** Given fuel level is forced to 2.0 gal, then the FUEL telltale lights amber while the other three dots stay dead-front dark.
- AE6. **Covers R10.** Given oil pressure 25 psi and coolant 220°F simultaneously, then the takeover shows OIL PRESSURE (higher priority), and clears to the prior view only when both conditions clear.
- AE7. **Covers R16.** Given the odometer reads 24,318 and power is cycled, then it resumes at 24,318; after `odo set 12000`, it resumes at 12,000.
- AE8. **Covers R2.** Given each mode's rendered screen is compared to its reference render, then layout proportions, colors, and type hierarchy visibly match at 1024×600.

### Scope Boundaries

- The two 5" side screens (ENGINE, TIMING/ROAD) — designed, explicitly Phase 2.
- All CAN and RaceCapture integration — the Coyote Gen 4 control pack, both PMU16s, GPS/lap timing, and CAN-driven mode switching arrive later behind the R12 data interface.
- Units toggle and accent variants from the mock's Tweaks panel — MPH and gold are final.
- Physical bezel LEDs (turn signals, future telltale LEDs) — hardware, not screens.

#### Deferred to Follow-Up Work

- Raising SPI clock above 8 MHz after `EVE_init()` (BT817 allows up to 30 MHz post-init) — not needed for 30 fps; revisit if frame budget ever tightens.
- Compiling static DL fragments into RAM_G and replaying via `CMD_APPEND` — an optimization with no current need.
- `EVE_busy()` timeout hardening (carried over from the splash round's advisory finding).

### Dependencies / Assumptions

- TRACK mode's lap/delta/position values are simulator fiction until RaceCapture integration — convincing for demos, meaningless on a real track day.
- Custom fonts fit RAM_G comfortably: the dash uses no bitmap assets and the splash renders from panel flash (KTD11), so the full 1 MiB belongs to font glyphs.
- The Teensy 4.1's EEPROM emulation (4284 bytes, wear-leveled flash) handles odometer persistence.
- Vehicle constants and warning thresholds are taken verbatim from the vendored design README (redline 8000, shift 7600, T56 ratios, 3.73 final, 26" tires, threshold table).
- Saira Condensed and Chakra Petch are OFL-licensed (Google Fonts) and safe to vendor and convert.

---

## Planning Contract

### Product Contract preservation

Product Contract changed in one place:

- **R8** — telltales gain a third visual state ("no data": muted gray, distinct from dead-front dark and lit) beyond the spec's two. Reason: R11's own validity model — with only two states, a lost sensor renders identically to "confirmed OK", silently defeating the telltale's purpose.

One user-directed architecture addition beyond the original contract: the boot splash's assets migrate from Teensy-PROGMEM-to-RAM_G into the panel's onboard QSPI flash (KTD11, U12). This is a storage rearchitecture of the already-shipped splash — its animation, themes, and timing contract stay identical — and it is what makes R17's direct crossfade possible alongside the dash fonts (an earlier draft of this plan had to substitute a fade-through-black because splash assets and fonts could not share RAM_G).

Everything else is unchanged.

### Key Technical Decisions

- **KTD1 — Fonts: legacy 148-byte EVE bitmap fonts in L4, built by our own converter.** `tools/make_dash_fonts.py` (Pillow + numpy, run under WSL, deterministic like `tools/make_splash_assets.py`) rasterizes vendored TTFs into fixed-cell L4 glyph sheets (4 bpp — half the RAM_G of L8, visually fine for anti-aliased text) plus the legacy 148-byte metric block per font instance (128 width bytes, format, stride, width, height, glyph pointer — layout per BT81x Programming Guide §5.4.1). Glyphs are stored only for each instance's character subset (digits + punctuation for numeral fonts; A–Z0–9 for label fonts); `firstchar` goes to `EVE_cmd_setfont2()`. The legacy block only addresses character codes 0–127, so the two non-ASCII glyphs are remapped into unused ASCII cells — the degree-sign artwork renders into `F_VAL`'s `*` cell and the middle-dot artwork into `F_LABEL`'s `;` cell — and firmware strings use the remapped bytes; the converter asserts every glyph code in every subset is < 128. The design's letter-spacing is baked into the width bytes (EVE has no tracking control). Glyph sheets are zlib-compressed into PROGMEM headers and uploaded at boot with `EVE_cmd_inflate()`; metric blocks (with the boot-time RAM_G glyph address patched in) are written raw with `EVE_memWrite_flash_buffer()`. Fonts register on bitmap handles 0–14 (15 is widget scratch, 16–31 are ROM fonts); `CMD_SETFONT2` emits DL commands, so each frame's burst re-registers the fonts it uses (~5 words each). The extended/xfont format (UTF-8) is deliberately not used — ASCII subsets suffice.
- **KTD2 — Arcs and needles are polylines; no CMD_ARC on BT817.** Verified: `CMD_ARC` exists only on BT82x; the vendored library has no arc command. The 240° sweeps render as `EVE_LINE_STRIP` polylines with `LINE_WIDTH` round caps (stroke ≈ 9–10 design units scaled), one segment per ~3° (≤81 vertices for a full sweep), endpoints precomputed with float `sinf/cosf` on the 600 MHz M7 (the library's `EVE_polar_cartesian` is 1°/int8 resolution — too coarse). Needles are 2-vertex `EVE_LINES` with round caps. All gauge geometry uses `VERTEX2F` (±1023.9 px at 1/16-px precision) — `VERTEX2II` tops out at x=511 and cannot address the right half of the panel. Coordinates are clamped on-screen before emission (the splash round's wraparound lesson).
- **KTD3 — Boot handoff: direct crossfade, fonts uploaded before the splash starts.** With splash assets living in panel flash (KTD11), RAM_G is empty at boot: `setup()` runs `EVE_init()` → `EVE_init_flash()` (attach + flashfast; `REG_FLASH_SIZE` printed in the banner) → font upload into RAM_G (~0.3–0.6 s at 8 MHz for ~250 KB — replaces today's comparable splash-PNG upload, so time-to-splash stays roughly what it is now; the backlight is dark until the first splash frame either way) → `run_splash()` renders from flash → the existing 400 ms crossfade ramp blends splash out / dash in, exactly the R17 contract. If a font upload faults (`EVE_busy()` reports and auto-recovers coprocessor faults), retry that instance once; on repeat failure, log the error over serial and boot the dash anyway with ROM font 31 substituted for the failed instance — a degraded dash beats a black panel in a car. If `EVE_init_flash()` fails (no/corrupt flash), skip the splash entirely and go straight to the dash, logging the failure — the dash never depends on flash. Before the crossfade begins, the channel struct is explicitly initialized (validity bitmask all-invalid, then the simulator stepped once) so the first visible dash frame shows plausible values and an uninitialized channel can never flash a false alarm takeover at power-up.
- **KTD4 — Data interface: a channels struct with validity bits.** `MustangDash/dash_data.h` defines only the channels a Phase-1 renderer or alarm consumes (rpm, speed_mph, ect_f, oil_temp_f, oil_press_psi, volts, fuel_gal, lap_ms, last_ms, best_ms, delta_s, ambient_f) as a plain struct plus a per-channel validity bitmask and the dash mode. Channels with no current consumer (AFR, IAT, fuel pressure, throttle/brake, lap number, position — all 5"-screen or Phase-2 material) are deliberately left out; adding a field when a consumer arrives is a one-line change, per the plan's own no-current-need precedent. Producers fill it: the simulator now, CAN decoders later. Renderers read only this struct; an invalid channel renders `--` and can never assert an alarm (R11). One rendering convention covers every non-text element backed by an invalid channel (a needle has no `--` glyph): needles and value arcs park at their zero/rest position at dead-front opacity, bar fills render empty, shift lights render dark, and telltales render a distinct muted "no data" state (dim gray dot + label, visibly different from both dead-front dark and lit) so a lost sensor is never mistaken for "confirmed OK" — a telltale's whole job is surfacing faults.
- **KTD5 — Simulator: pure host-testable header, display units.** `MustangDash/dash_sim.h` steps the state with an injected `dt_ms` (no `millis()` inside): RPM ramps through gears using the vehicle constants (shift at ~7900 → drop to ~5200; per-gear speed from `MPH = RPM × 26 / (ratio × 3.73 × 336)`), temps warm from ambient toward operating values then oscillate gently, oil pressure tracks RPM, ~62 s lap cycle updates last/best, delta is a smooth ±0.8 s blend, fuel burns down, STREET mode cruises (~2500 RPM, ~60 MPH). All values in display units (MPH, °F, psi, gal, V). Deterministic given the same seed/dt sequence — host-testable.
- **KTD6 — Serial protocol: newline-terminated ASCII lines, parser as a pure header.** On the existing USB serial (115200): `set <channel> <value>`, `clear <channel>` (marks the channel invalid), `mode track|street`, `alarm oilp|oilt|clt|off` (forces the matching channel past/off its threshold), `odo set <miles>`, `sim on|off` (resume pure simulation / freeze), `status`, `help`. Overrides are sticky per channel until `clear`-ed or `sim on`. Every command is acked with one `ok …` or `err …` line; the firmware prints nothing else after boot, so the boot banner and RAM_G diagnostics coexist untouched. `MustangDash/dash_serial.h` holds the tokenizer/parser as pure functions (line in → command struct out) — host-testable; only the thin `Serial.available()` pump and command application live in the `.ino`.
- **KTD7 — Odometer: raw `avr/eeprom.h` C API, tenth-mile integers.** The record `{magic, version, odo_tenths (uint32), trip_tenths (uint32), crc8}` lives at a fixed EEPROM offset. The raw C API (`eeprom_read_block`/`eeprom_write_block`) is used instead of the `EEPROM.h` class library because the offline sandbox toolchain vendors only `cores` + `SPI` (the class lib would silently break that build path); the Teensy 4.1 core's emulation is wear-leveled flash, 4284 bytes. Write cadence: on each 0.1 mi increment (~every 6 s at 60 MPH) and on `odo set`; a CRC-invalid or blank record initializes to zero.
- **KTD8 — Frame pipeline: one DMA burst per frame, free-running.** `loop()` becomes: pump serial → step simulator/apply overrides (dt from `millis()`) → integrate odometer → evaluate alarms → build the frame as a single burst (`EVE_start_cmd_burst()` … `_burst` calls … `EVE_end_cmd_burst()`), then poll `EVE_busy()` before starting the next. The Teensy DMA buffer caps a burst at 1024 words; the STREET frame (the heaviest: two arcs + ticks + labels + needles + telltales + odometer + font registrations) is estimated ≈ 500–700 words. If measurement shows growth past ~900 words, split the frame into two bursts with an `EVE_busy()` wait between — a known, planned fallback, not a redesign, and one the first full STREET frame may need immediately (an independent estimate puts it at 650–750 words before headroom). The 8 KB display list (2048 entries) is the second budget; text widgets expand per glyph. DL usage is measured without violating KTD6's quiet-serial contract: during the boot handoff (before the crossfade) the firmware builds one un-swapped throwaway DL per mode, reads `REG_CMD_DL`, and prints both figures as part of the boot banner; after boot, DL/burst word counts are reported only inside the `status` ack.
- **KTD9 — Layout: mock coordinates × (1024/620, 600/400) as named constants.** The mock draws the 7" at 620×400; positions and rectangular extents in `MustangDash/dash_layout.h` are the mock values scaled per-axis by 1.652/1.5 (computed at build time via macro helpers, values rounded to int px). Rotationally symmetric dimensions — gauge radii, tick radii, needle length, LED/point diameters, arc stroke widths — scale by the single Y factor 1.5 so the 240° gauges stay circular (per-axis scaling would stretch them into ellipses ~10% wider than tall and visibly fail AE8); gauge centers still place by the per-axis factors. The layout header names the split explicitly (e.g. `LX()`/`LY()` for positions, `LR()` for radial dimensions). The non-linear speedo mapping is exactly the mock's: `f(v) = (v/140)·0.8235` for v ≤ 140, else `0.8235 + ((v−140)/20)·0.0588`; sweep angle `a = 210° − f·240°`. Colors come verbatim from the design tokens; the screen background is flat `#080b0f` (explicitly sanctioned by the spec in lieu of the radial gradient). The alarm background alternates a `CMD_GRADIENT` vertical `#d92020 → #700c0c` with near-black `#260606`.
- **KTD11 — Splash assets live in the panel's QSPI flash as ASTC, rendered directly from flash.** The RVT70H module carries a NOR flash chip on the BT817's QSPI (per Riverdi's EVE4 product documentation; exact size probed at boot via `REG_FLASH_SIZE`). Splash assets convert to ASTC-compressed bitmaps (the only format the BT817 renders straight from flash — no RAM_G residency at all): detail elements (emblem, wordmark, bars, year, checker pieces) at ASTC 4×4, soft gradient backgrounds at ASTC 8×8 and now at **full 1024×600 resolution** (the old 512×300 + 2× bilinear trick existed only to fit RAM_G). The float-reconstruction blur from the banding fix is retained ahead of encoding; the Bayer dither is dropped for flash assets (ordered noise fights block compression) — banding re-checked on the panel. Provisioning: the converter emits a single flash image (BT817 unified blob in the first 4096 bytes, then the asset pack for **all three themes** with a trailing version/CRC marker); the firmware embeds it in PROGMEM and runs `CMD_FLASHUPDATE` at boot only when the stored marker differs (first boot ~seconds, every later boot a no-op). Rendering uses `EVE_cmd_setbitmap`/`BITMAP_EXT_FORMAT` with flash-addressed sources (32-byte blocks per the library's ASTC notes); the splash timeline, draw order, and theme selection are untouched. Net Teensy flash: the ~206 KB of splash PNG headers are deleted; the embedded flash image adds ~1 MB (all three themes, full-res) — ~13% of the 8 MB part.
- **KTD10 — Every pure computation lives in a host-testable header.** Gauge fractions/angles, shift-light count and flash state, threshold→color classification, delta-bar geometry, lap-time formatting, odometer integration, sim stepping, and serial parsing all follow the `splash_timeline.h` pattern (stdint-only, `static inline`, no Arduino/EVE includes) with matching `tests/test_*.c` registered in `tests/run-tests.sh`. Every new `.ino` function gets an explicit forward prototype (offline ctags shim requires it).

### High-Level Technical Design

```mermaid
flowchart LR
    subgraph producers [Producers]
        SIM[dash_sim.h<br/>simulator]
        SER[dash_serial.h parser<br/>+ .ino serial pump]
        CAN[(CAN decoders<br/>Phase 2)]
    end
    subgraph state [Shared state]
        CH[dash_data.h<br/>DashChannels + validity + mode]
        ODO[odometer<br/>EEPROM record]
    end
    subgraph render [Per-frame render — one DMA burst]
        AL{alarm<br/>active?}
        TK[TRACK renderer]
        ST[STREET renderer]
        OV[Alarm takeover]
    end
    SIM --> CH
    SER -->|sticky overrides,<br/>mode, alarm, odo set| CH
    CAN -.-> CH
    CH --> AL
    CH --> ODO
    AL -->|no, mode=TRACK| TK
    AL -->|no, mode=STREET| ST
    AL -->|yes| OV
    TK & ST & OV --> DL[CMD_DLSTART … SWAP<br/>via burst + EVE_busy]
```

Boot sequence (KTD3/KTD11): `setup()` → serial wait + banner → `EVE_init()` → `EVE_init_flash()` + provision check (`CMD_FLASHUPDATE` when the asset marker differs) → upload fonts to RAM_G (inflate glyphs + write metric blocks, log totals) → throwaway per-mode DLs for the banner's DL-usage figures → `run_splash()` rendering ASTC bitmaps from flash → direct 400 ms crossfade into the dash → `loop()` free-runs the pipeline above.

### RAM_G and Flash Budget

Font instances (L4 = 0.5 byte/px; cell sizes are plan-time estimates the converter will print exactly):

| Instance | Face / weight | ~px height (1024×600) | Glyph set | Est. RAM_G |
|---|---|---|---|---|
| `F_HERO` | Saira Cond 700 | ~216 | `0-9`, `-` (11) | ~130 KB |
| `F_BIG` | Saira Cond 700 | ~96 | `0-9 :.-` (14) | ~30 KB |
| `F_MID` | Saira Cond 600 | ~52 | `0-9 :.-+` (15) | ~11 KB |
| `F_VAL` | Saira Cond 600 | ~32 | `0-9 :.-+°` (16) | ~5 KB |
| `F_SMALL` | Saira Cond 600 | ~26 | `0-9 .` (11) | ~3 KB |
| `F_TITLE` | Chakra Petch 700 | ~72 | `A-Z` + space (27) | ~38 KB |
| `F_LABEL` | Chakra Petch 600 | ~20 | `A-Z0-9 /·"` (~40) | ~6 KB |
| `F_TINY` | Chakra Petch 500 | ~15 | same | ~4 KB |

Total ≈ **230–280 KB** decoded in RAM_G, which the fonts now have entirely to themselves — the splash renders from panel flash and touches RAM_G not at all (KTD11). The converter emits the exact packed table and the firmware logs `RAM_G: fonts N bytes (headroom M)` at boot, per the documented budgeting pattern. The alarm value (~174 px spec) renders in `F_HERO` — one shared hero instance instead of a ninth.

Panel flash layout (KTD11; sizes are plan-time estimates, the converter prints exact figures):

| Region | Content | Est. size |
|---|---|---|
| 0–4 KB | BT817 unified blob (flashfast driver) | 4 KB |
| asset pack | 3 × full-res 1024×600 bg @ ASTC 8×8 | ~460 KB |
| asset pack | detail elements (emblem, wordmark, bars, lines, years, checker) @ ASTC 4×4 | ~300–500 KB |
| trailer | version/CRC marker | bytes |

Teensy flash (`data`) change: −206 KB (splash PNG headers deleted) + ~1 MB (embedded flash image for provisioning) + 100–150 KB (zlib font glyphs) ≈ **net +0.9–1 MB** of the Teensy 4.1's 8 MB.

### Assumptions

Recorded per headless planning (no scoping confirmation was possible in pipeline mode); the splash-to-flash migration itself is a user decision, not an assumption:

- The panel's QSPI flash is populated and large enough (Riverdi's EVE4 documentation says every module carries one; size probed at boot via `REG_FLASH_SIZE`). If `EVE_init_flash()` fails on the bench, U12 falls back to the shipped RAM_G splash architecture and the boot handoff reverts to a fade-through-black — documented exit, not a redesign of the dash.
- ASTC 8×8 on the float-reconstructed full-res backgrounds is band-free enough on the panel (the Bayer-dither stage is dropped for flash assets; bench-verify, step up to 4×4 or 6×6 if gradients suffer).
- The simulator and thresholds operate in the README's display units (MPH, °F, psi); the mock's internal metric state is not replicated.
- The alarm value sharing `F_HERO` (~216 px vs the spec's ~174 px) is an acceptable substitution.
- Default boot mode is TRACK (the mock's default); `mode` changes are runtime-only (not persisted) until CAN owns the input.
- `tools/pony.py` stays in the tree as historical tooling; `MustangDash/pony_png.h` and the pony draw code are deleted.

### Risk Analysis & Mitigation

- **Burst/DL overflow as screens grow** (highest likelihood): STREET is estimated 500–700 words against a 1024-word burst and 2048-entry DL. Mitigations are designed in, not hoped for: per-frame word counter, one-time `REG_CMD_DL` log, and the planned two-burst split (KTD8). Trigger point: sustained > 900 words.
- **Font pipeline is the long pole** (highest impact): a wrong metric block renders garbage with no error. Mitigations: block-layout invariants host-tested (U2), one-font hardware smoke before building all instances (U6 execution note), ROM-font-31 degraded fallback on upload fault (KTD3).
- **EEPROM wear**: worst case ~1 write/6 s at highway speed = ~600/hr against a wear-leveled 4284-byte emulation spreading writes over 63 flash sectors — decades of margin; `odo set` misuse can't change the order of magnitude. Corrupt/blank records CRC-fail into a clean zero init (never garbage miles).
- **L4 legibility at small sizes**: 15–20 px labels may look thin; the converter keeps a per-instance L8 flag (Deferred Notes) with negligible budget impact.
- **Flash growth**: net ~+1 MB Teensy `data` (embedded panel-flash image + font glyphs, minus the deleted splash PNG headers) — ~13% of the Teensy 4.1's 8 MB; noted so the build-size invariant watchers aren't surprised.
- **Panel-flash provisioning**: a bad or interrupted `CMD_FLASHUPDATE` leaves a stale asset pack — the CRC marker catches it and the next boot re-provisions; a genuinely absent/dead flash chip degrades to skipping the splash (KTD3), never to a broken dash. ASTC encoding is pinned to one encoder version and single-threaded flags so the flash image is deterministic like every other generated asset.
- **Serial protocol vs. boot diagnostics**: collision avoided structurally — firmware emits nothing after boot except command acks (KTD6), so `/dash` reads are unambiguous.

---

## Implementation Units
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
