kms254/Mustang-Dash-Test/assets/splash/HANDOFF.md

# HANDOFF — Boot splash for 7" EVE4 dash display

## Task
Implement the 2-second animated boot splash described in `README.md` (same folder), then hold the final frame until the main dash UI takes over.

## Hardware context
- Display: 7" EVE4 module, BT817 controller, 1024×600, SPI interface
- Host MCU: **TODO — fill in (e.g. STM32F4, ESP32, Arduino Mega + shield)**
- EVE library: **TODO — fill in (e.g. Bridgetek EVE_HAL, Rudolph Riedel FT800-FT813, Matrix Orbital EVE lib)**
- Theme chosen: **TODO — blue / red / checkered**
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
