kms254/Mustang-Dash-Test/kicad/board3/EASYEDA_MODELS/DC-IN-TH_DC-005-2.step

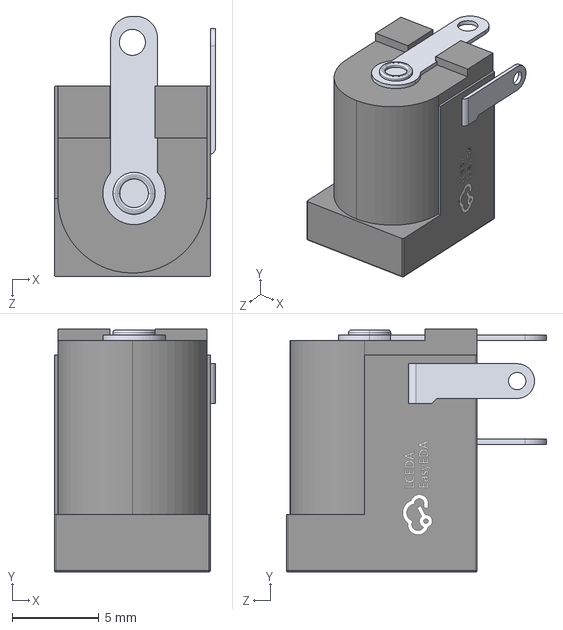
[picture p20: CAD file, 2026-07-29]
kicad/board3/EASYEDA_MODELS/DC-IN-TH_DC-005-2.step
9.30 x 14.0 x 15.0 mm
