kms254/Mustang-Dash-Test/kicad/board3/EASYEDA_MODELS/LQFP-144_L20.0-W20.0-P0.50-LS22.0-BL.step

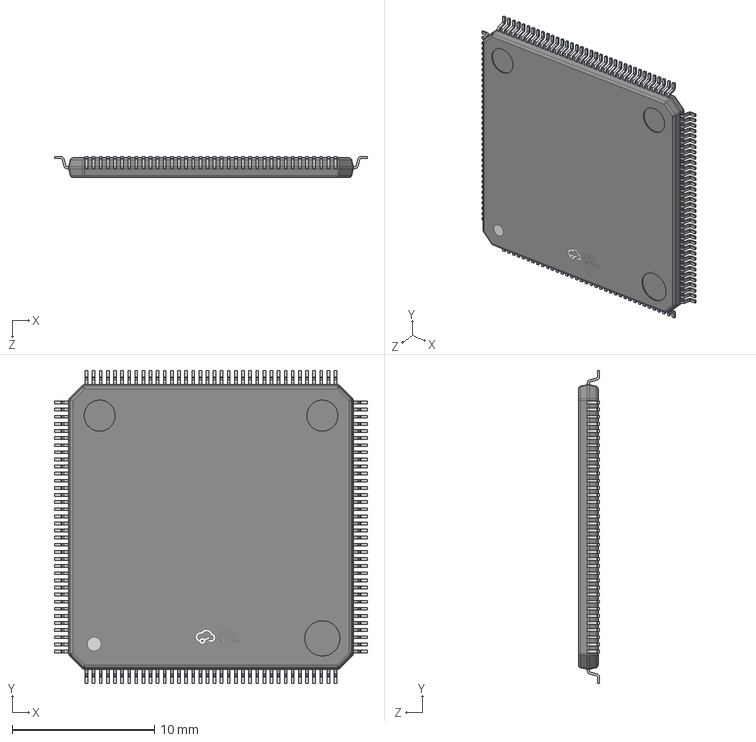
[picture p21: CAD file, 2026-07-29]
kicad/board3/EASYEDA_MODELS/LQFP-144_L20.0-W20.0-P0.50-LS22.0-BL.step
22.0 x 22.0 x 1.50 mm
