kms254/Mustang-Dash-Test/kicad/board3/EASYEDA_MODELS/SOIC-18_L11.6-W7.5-H2.7-LS10.3-P1.27.step

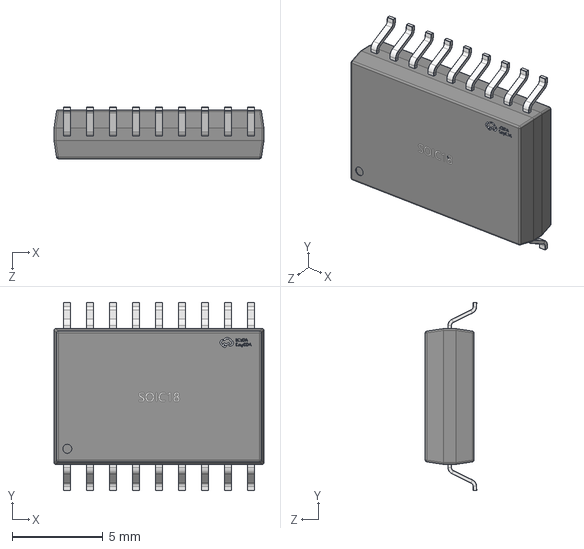
[picture p22: CAD file, 2026-07-29]
kicad/board3/EASYEDA_MODELS/SOIC-18_L11.6-W7.5-H2.7-LS10.3-P1.27.step
11.6 x 10.4 x 2.85 mm
