kms254/Mustang-Dash-Test/kicad/board3/EASYEDA_MODELS/CRYSTAL-SMD_4P-L3.2-W2.5-BL.step

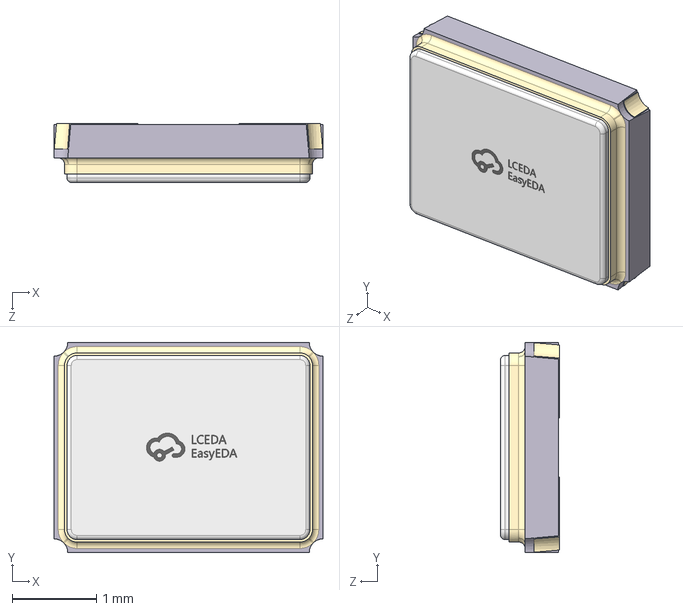
[picture p23: CAD file, 2026-07-29]
kicad/board3/EASYEDA_MODELS/CRYSTAL-SMD_4P-L3.2-W2.5-BL.step
3.20 x 2.50 x 0.701 mm
