kms254/Mustang-Dash-Test/kicad/board3/EASYEDA_MODELS/WSON-8_L8.0-W6.0-P1.27-TL-EP.step

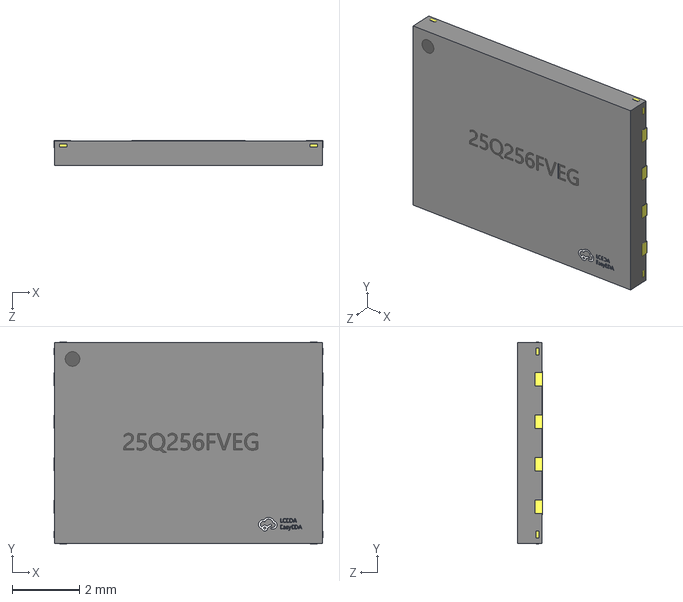
[picture p24: CAD file, 2026-07-29]
kicad/board3/EASYEDA_MODELS/WSON-8_L8.0-W6.0-P1.27-TL-EP.step
8.02 x 6.02 x 0.751 mm
