kms254/Mustang-Dash-Test/kicad/board3/EASYEDA_MODELS/ESSOP-10_L4.9-W3.9-P1.0-LS6.0-TL-EP.step

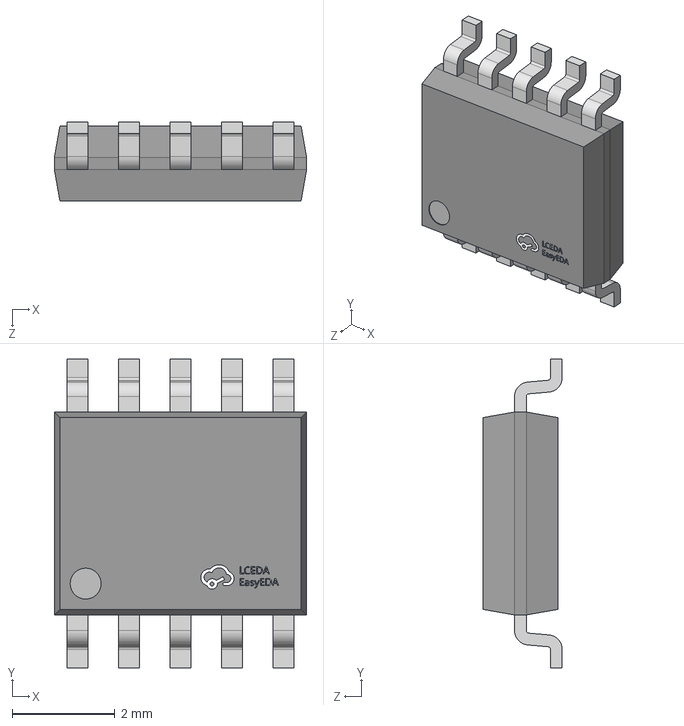
[picture p25: CAD file, 2026-07-29]
kicad/board3/EASYEDA_MODELS/ESSOP-10_L4.9-W3.9-P1.0-LS6.0-TL-EP.step
4.90 x 6.00 x 1.54 mm
