kms254/Mustang-Dash-Test/kicad/board3/EASYEDA_MODELS/SOP-8_L5.0-W3.8-P1.27-LS6.0-BL.step

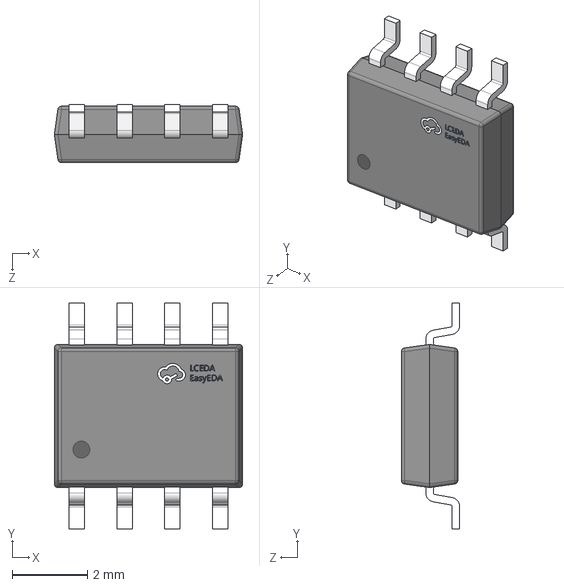
[picture p26: CAD file, 2026-07-29]
kicad/board3/EASYEDA_MODELS/SOP-8_L5.0-W3.8-P1.27-LS6.0-BL.step
5.00 x 6.00 x 1.55 mm
