kms254/Mustang-Dash-Test/MustangDash/dash_data.h

/* dash_data.h -- the dash's single data interface (KTD4).
 *
 * Pure header: stdint/stdbool only, no Arduino/EVE includes, host-testable.
 * Producers -- dash_sim.h and now CAN decoders (dash_can_ford.h is the first
 * live dialect; RaceCapture and PMU16 follow as peers) -- fill DashState.ch
 * and set validity bits; renderers read only this struct. An invalid channel
 * renders `--` (text) or the dead-front convention (graphics) and can never
 * assert an alarm (R11).
 *
 * CAN ownership (Ford plan KTD5): a decoder that accepts a frame writes the
 * channel and sets its bit in `can_owned`, locking the simulator out
 * (dash_ch_sim_owned below). The Ford dialect claims RPM, SPEED, ECT, OILT,
 * OILP, VOLTS, AFR_L, AFR_R, FUELP -- 9 of the 26. Invariant: a channel may
 * be claimed by AT MOST ONE CAN dialect; a future dialect carrying an
 * already-claimed channel (RaceCapture broadcasts GPS speed) requires
 * revisiting the mask design before it lands. Only the decoder and its
 * expiry pass manage `can_owned` -- serial's `sim on` wipes the serial masks
 * below but never touches it.
 *
 * Override semantics (KTD6):
 *  - `set <ch> <v>`  -> value written, valid bit set, override bit set;
 *                       the simulator must not touch overridden channels.
 *  - `clear <ch>`    -> valid bit dropped, cleared bit set; stays invalid
 *                       across sim steps until `sim on` or a new `set`.
 *  - `sim on`        -> override and cleared masks wiped; sim owns all
 *                       channels again. `sim off` freezes stepping entirely.
 */

#ifndef DASH_DATA_H
#define DASH_DATA_H

#include <stdint.h>
#include <stdbool.h>

/* Channel ids -- one bit each in the valid/override/cleared masks.
 * Phase-1 set only (plan KTD4): channels with no current renderer or alarm
 * consumer are deliberately absent. */
enum {
    DASH_CH_RPM = 0,
    DASH_CH_SPEED,   /* MPH */
    DASH_CH_ECT,     /* coolant, degF */
    DASH_CH_OILT,    /* oil temperature, degF */
    DASH_CH_OILP,    /* oil pressure, psi */
    DASH_CH_VOLTS,
    DASH_CH_FUEL,    /* gallons */
    DASH_CH_DELTA,   /* lap delta, seconds, negative = ahead */
    DASH_CH_LAP,     /* current lap time, ms */
    DASH_CH_LAST,    /* last lap, ms */
    DASH_CH_BEST,    /* best lap, ms */
    DASH_CH_AMBIENT, /* degF */
    /* Phase-2 set (plan KTD5): side-screen channels. */
    DASH_CH_AFR_L,    /* air/fuel ratio, left bank */
    DASH_CH_AFR_R,    /* air/fuel ratio, right bank */
    DASH_CH_IAT,      /* intake air temperature, degF */
    DASH_CH_FUELP,    /* fuel pressure, psi */
    DASH_CH_THROTTLE, /* throttle position, percent */
    DASH_CH_BRAKE,    /* brake position, percent */
    DASH_CH_LAPN,     /* lap number */
    DASH_CH_POS,      /* race position */
    DASH_CH_PRED,     /* predicted lap time, ms */
    DASH_CH_TIME,     /* minutes since midnight, 0..1439 */
    DASH_CH_PUMP,     /* PMU output: fuel pump, amps (0 = off) */
    DASH_CH_FAN1,     /* PMU output: fan 1, amps (0 = off) */
    DASH_CH_FAN2,     /* PMU output: fan 2, amps (0 = off) */
    /* Session elapsed time, ms, TRACK-only. Counts UP: no surveyed racing
     * platform (Bosch DDU, MoTeC C127, AiM) ships a race COUNTDOWN -- Bosch's
     * only countdown is a pit-lane minimum-time timer -- and MoTeC's own
     * documentation describes a count-up timer as how a driver knows how much
     * time is left. See dash_sim.h's session cycle for its only reset. */
    DASH_CH_SESSION,
    DASH_CH_COUNT
};

#define DASH_CH_BIT(ch) ((uint32_t) (1U << (ch)))
/* 1ULL: at DASH_CH_COUNT == 32 the uint32 form (1U << 32) is UB -- the
 * <= 32 guard in tests would green-light exactly the count that breaks
 * the macro (review finding; the CAN round grows the enum toward it). */
#define DASH_CH_ALL ((uint32_t) ((1ULL << DASH_CH_COUNT) - 1ULL))

typedef enum {
    DASH_MODE_TRACK = 0,
    DASH_MODE_STREET = 1,
} DashMode;

typedef struct {
    float rpm;
    float speed_mph;
    float ect_f;
    float oil_temp_f;
    float oil_press_psi;
    float volts;
    float fuel_gal;
    float delta_s;
    uint32_t lap_ms;
    uint32_t last_ms;
    uint32_t best_ms;
    float ambient_f;
    /* Phase-2 fields (plan KTD5). */
    float afr_l;
    float afr_r;
    float iat_f;
    float fuel_press_psi;
    float throttle_pct;
    float brake_pct;
    uint32_t lap_n;
    uint32_t pos;
    uint32_t pred_ms;
    uint32_t time_min;
    float pump_a;
    float fan1_a;
    float fan2_a;
    uint32_t session_ms;
} DashChannels;

typedef struct {
    DashChannels ch;
    uint32_t valid;      /* DASH_CH_BIT() per channel */
    uint32_t overridden; /* serial `set` freezes these against the sim */
    uint32_t cleared;    /* serial `clear` holds these invalid */
    uint32_t can_owned;  /* CAN-decoder-claimed channels: sim locked out;
                          * managed only by dash_can_ford.h (decode + expiry),
                          * zero at boot via dash_state_init's {0} */
    DashMode mode;
    bool sim_frozen;     /* `sim off`: hold current values, stop stepping */
    uint8_t tt_signals;  /* CAN-sourced telltales, as PHYSICAL positions
                          * (TT1..TT8 = bit 0..7) rather than warning
                          * conditions: the body/PCM signals the firmware
                          * cannot compute -- blinkers, headlights, high
                          * beam, parking brake, CEL/MIL. See
                          * docs/hardware/board3-telltale-legend.md.
                          *
                          * The seam only; no producer exists yet. A future
                          * RaceCapture dialect owns the five body signals
                          * and the Ford dialect the MIL, each responsible
                          * for its own staleness/expiry exactly as
                          * can_owned channels are -- this layer never
                          * ages a bit out. Zero at boot via
                          * dash_state_init's {0}, so an unwired bench
                          * simply shows those positions dark. */
    uint8_t tt_forced;   /* serial `tt` bench overlay: lamp bits forced ON,
                          * OR'd over the computed mask by
                          * dash_telltale_mask(). `tt n off` releases the
                          * force only -- it cannot suppress a live alarm
                          * lamp. Zero at boot via dash_state_init's {0}. */
} DashState;

static inline bool dash_ch_valid(const DashState *s, uint8_t ch)
{
    return (s->valid & DASH_CH_BIT(ch)) != 0U;
}

/* True when the simulator may write this channel this step: neither serial
 * (overridden/cleared) nor a CAN decoder (can_owned) holds it -- the sim is
 * the producer of last resort. */
static inline bool dash_ch_sim_owned(const DashState *s, uint8_t ch)
{
    return ((s->overridden | s->cleared | s->can_owned) & DASH_CH_BIT(ch)) == 0U;
}

static inline void dash_ch_set(DashState *s, uint8_t ch, float v)
{
    switch (ch) {
        case DASH_CH_RPM: s->ch.rpm = v; break;
        case DASH_CH_SPEED: s->ch.speed_mph = v; break;
        case DASH_CH_ECT: s->ch.ect_f = v; break;
        case DASH_CH_OILT: s->ch.oil_temp_f = v; break;
        case DASH_CH_OILP: s->ch.oil_press_psi = v; break;
        case DASH_CH_VOLTS: s->ch.volts = v; break;
        case DASH_CH_FUEL: s->ch.fuel_gal = v; break;
        case DASH_CH_DELTA: s->ch.delta_s = v; break;
        case DASH_CH_LAP: s->ch.lap_ms = (uint32_t) v; break;
        case DASH_CH_LAST: s->ch.last_ms = (uint32_t) v; break;
        case DASH_CH_BEST: s->ch.best_ms = (uint32_t) v; break;
        case DASH_CH_AMBIENT: s->ch.ambient_f = v; break;
        case DASH_CH_AFR_L: s->ch.afr_l = v; break;
        case DASH_CH_AFR_R: s->ch.afr_r = v; break;
        case DASH_CH_IAT: s->ch.iat_f = v; break;
        case DASH_CH_FUELP: s->ch.fuel_press_psi = v; break;
        case DASH_CH_THROTTLE: s->ch.throttle_pct = v; break;
        case DASH_CH_BRAKE: s->ch.brake_pct = v; break;
        case DASH_CH_LAPN: s->ch.lap_n = (uint32_t) v; break;
        case DASH_CH_POS: s->ch.pos = (uint32_t) v; break;
        case DASH_CH_PRED: s->ch.pred_ms = (uint32_t) v; break;
        case DASH_CH_TIME: s->ch.time_min = (uint32_t) v; break;
        case DASH_CH_PUMP: s->ch.pump_a = v; break;
        case DASH_CH_FAN1: s->ch.fan1_a = v; break;
        case DASH_CH_FAN2: s->ch.fan2_a = v; break;
        case DASH_CH_SESSION: s->ch.session_ms = (uint32_t) v; break;
        default: return;
    }
    s->valid |= DASH_CH_BIT(ch);
}

/* Put a channel BACK to invalid, so it renders `--` / dead-front again.
 *
 * dash_ch_set is one-way -- it only ever raises the valid bit -- so once the
 * simulator published a channel nothing it could do would take it back. It
 * needs to: DELTA has no meaning before a reference lap exists, and publishing
 * a fabricated zero instead of dead-fronting would be a lie the renderer has
 * no way to spot (U5).
 *
 * Guarded by the SAME ownership rule as writing (dash_ch_sim_owned), because
 * dead-fronting a channel is a write in every sense that matters:
 *  - overridden: the operator's forced value stays valid and untouched;
 *  - cleared:    already invalid, and the sticky cleared bit is left alone;
 *  - can_owned:  a CAN-fresh channel is not the sim's to dead-front.
 * This is the SIM-facing variant: the CAN decoder has its own
 * (dash_can_ford_invalidate), which honors only the serial masks -- this one
 * would silently no-op on the CAN-owned channels it must dead-front.
 * The value itself is never disturbed -- only the valid bit moves. */
static inline void dash_ch_invalidate(DashState *s, uint8_t ch)
{
    if (ch >= DASH_CH_COUNT) { return; }
    if (!dash_ch_sim_owned(s, ch)) { return; }
    s->valid = (uint32_t) (s->valid & ~DASH_CH_BIT(ch));
}

static inline float dash_ch_get(const DashState *s, uint8_t ch)
{
    switch (ch) {
        case DASH_CH_RPM: return s->ch.rpm;
        case DASH_CH_SPEED: return s->ch.speed_mph;
        case DASH_CH_ECT: return s->ch.ect_f;
        case DASH_CH_OILT: return s->ch.oil_temp_f;
        case DASH_CH_OILP: return s->ch.oil_press_psi;
        case DASH_CH_VOLTS: return s->ch.volts;
        case DASH_CH_FUEL: return s->ch.fuel_gal;
        case DASH_CH_DELTA: return s->ch.delta_s;
        case DASH_CH_LAP: return (float) s->ch.lap_ms;
        case DASH_CH_LAST: return (float) s->ch.last_ms;
        case DASH_CH_BEST: return (float) s->ch.best_ms;
        case DASH_CH_AMBIENT: return s->ch.ambient_f;
        case DASH_CH_AFR_L: return s->ch.afr_l;
        case DASH_CH_AFR_R: return s->ch.afr_r;
        case DASH_CH_IAT: return s->ch.iat_f;
        case DASH_CH_FUELP: return s->ch.fuel_press_psi;
        case DASH_CH_THROTTLE: return s->ch.throttle_pct;
        case DASH_CH_BRAKE: return s->ch.brake_pct;
        case DASH_CH_LAPN: return (float) s->ch.lap_n;
        case DASH_CH_POS: return (float) s->ch.pos;
        case DASH_CH_PRED: return (float) s->ch.pred_ms;
        case DASH_CH_TIME: return (float) s->ch.time_min;
        case DASH_CH_PUMP: return s->ch.pump_a;
        case DASH_CH_FAN1: return s->ch.fan1_a;
        case DASH_CH_FAN2: return s->ch.fan2_a;
        case DASH_CH_SESSION: return (float) s->ch.session_ms;
        default: return 0.0f;
    }
}

/* Boot state: everything invalid, sim running, TRACK default (KTD3). */
static inline void dash_state_init(DashState *s)
{
    const DashState zero = {0};
    *s = zero;
    s->mode = DASH_MODE_TRACK;
}

#endif /* DASH_DATA_H */
