kms254/Mustang-Dash-Test/tools/kicad_silk_trim.py

#!/usr/bin/env python3
"""Trim silkscreen lines back from solder-mask apertures.

    python tools/kicad_silk_trim.py BOARD.kicad_pcb            # report
    python tools/kicad_silk_trim.py BOARD.kicad_pcb --apply    # edit in place

Why this exists
---------------
JLCPCB wants 0.15 mm between silkscreen and a pad. Board3's imported footprints
draw body outlines straight past their pads, so **233 silk/pad pairs over 169
shapes** sat 0.031 to 0.1495 mm away -- every one a near miss, none an actual
overlap (verified uncapped: 0 pairs at or below 0.0000 mm).

That figure used to read "199 objects", which was `kicad-cli`'s per-error-code
report limit rather than a count -- see
docs/solutions/developer-experience/a-count-at-the-report-limit-is-not-a-measurement.md.
Measure the geometry, not the report, whenever the number is load-bearing.

Nothing caught it. The board's own .kicad_pro carries `min_silk_clearance: 0.15`
and `silk_over_copper: warning`, and KiCad runs NO silk test at all unless a
`silk_clearance` rule exists in the .kicad_dru -- so a setting that looks
configured was enforcing nothing, and DRC reported 0 while the fab reported 81.
The gerbers already pass --subtract-soldermask, so the fab clips the ink and the
board is buildable; what is wrong is the design, which claims markings it will
not get.

Trimming, not moving
--------------------
The outline is cut where it runs past a pad, leaving the surviving pieces where
they are. Moving it outward would keep it continuous at the cost of drawing a
body larger than the part -- which is what the assembler reads, and this board is
dense enough that courtyards already touch. Trimming also makes the design match
what --subtract-soldermask produces, instead of diverging from it.

Method
------
The keepout is each pad's mask aperture (its effective polygon; this board's
solder-mask expansion is 0) inflated by the clearance plus half the silk line
width, because the constraint is edge-to-edge and the stored geometry is a
centreline. Each line is walked in fine steps, exact point-to-polygon distance
at every step, and every blocked/clear boundary is refined by bisection to
0.1 um. `GetEffectiveShape().Collide()` is deliberately not used -- CLAUDE.md
records it under-covering segment midpoints, which is exactly this query.

Polygons are reported, not touched: a polygon on silk is usually a polarity
band or a pin-1 marker, where cutting destroys the meaning the marker exists to
carry. Lines, circles and arcs are trimmed.

Scope: own pads, not every nearby pad
-------------------------------------
`--scope own` (the default) trims a footprint's silk against ITS OWN pads only.
That is not a simplification -- it is what makes the fix mirrorable. Trimming
each placement against whatever happens to be next to it produces per-placement
geometry: the first attempt left `C0805` with 11 instances and 4 distinct silk
outlines, which is correct per-board geometry and impossible for one library
definition to hold. Own-pad geometry is a property of the TYPE, identical for
every placement, so `kicad_silk_mirror.py` can write it back.

Measured on Board3 before choosing this: of 169 violating silk shapes, 146 hit
only their own pads, 5 hit only a neighbour's (X1 x3, R9 x2) and none hit both.
So own-pad scope reaches 96% of the footprint-owned work, and the residue is
two footprints rather than a structural problem. `--scope all` keeps the old
behaviour for measuring that residue; it must not be used on anything destined
for a library.

Board-level graphics have no library half, so they are always trimmed against
every nearby pad regardless of --scope. There is no type for them to diverge
from.
"""
from __future__ import annotations

import argparse
import collections
import math
import sys

import pcbnew

NM = 1e6
CLEARANCE_MM = 0.15
# GetEffectivePolygon() returns a polygon INSCRIBED in a round pad, so its
# corners sit inside the true arc and every distance measured against it runs a
# few microns optimistic. Trimming to exactly 0.15 mm therefore left residual
# violations of ~3.8 um -- correct arithmetic against a slightly wrong shape.
# Cut this much further so the approximation cannot decide the outcome.
MARGIN_MM = 0.02
# Thinnest line the fab will print. JLCPCB publishes 0.15 mm; this carries a
# little over it so a narrowed line does not land exactly on the limit and
# become a width violation instead of a clearance one. The two requirements
# pull against each other -- JLC already flags 25 items on this board for being
# THINNER than its minimum -- so a shape needs centreline room for both or it
# cannot be fixed by width at all.
MIN_SILK_WIDTH_MM = 0.16
STEP_NM = 5_000          # 5 um walk
REFINE_NM = 100          # bisect to 0.1 um
MIN_KEEP_NM = 200_000    # drop surviving stubs under 0.2 mm -- ink noise

_KEEPALIVE: list = []    # removed items must outlive SaveBoard (SWIG lifetime)


def poly_points(pad, layer) -> list[list[tuple[int, int]]]:
    """Outline point lists of a pad's effective polygon, in board coordinates.

    GetEffectivePolygon() takes a layer in KiCad 10 and raises without one. Do
    NOT wrap this in a bare except: an earlier revision did, every pad silently
    returned no rings, and the tool cheerfully reported zero work to do on a
    board with 233 violating pairs. A geometry helper that returns "nothing" on
    error is indistinguishable from one that found nothing.
    """
    ps = pad.GetEffectivePolygon(layer)
    out = []
    for i in range(ps.OutlineCount()):
        o = ps.Outline(i)
        pts = [(o.CPoint(j).x, o.CPoint(j).y) for j in range(o.PointCount())]
        if len(pts) >= 3:
            out.append(pts)
    return out


def dist_point_poly(px: float, py: float, rings) -> float:
    """Exact distance from a point to a polygon (0 when inside)."""
    best = float("inf")
    for pts in rings:
        inside = False
        n = len(pts)
        for i in range(n):
            ax, ay = pts[i]
            bx, by = pts[(i + 1) % n]
            # edge distance
            dx, dy = bx - ax, by - ay
            if dx or dy:
                t = ((px - ax) * dx + (py - ay) * dy) / float(dx * dx + dy * dy)
                t = 0.0 if t < 0 else (1.0 if t > 1 else t)
                cx, cy = ax + t * dx, ay + t * dy
            else:
                cx, cy = ax, ay
            d = math.hypot(px - cx, py - cy)
            if d < best:
                best = d
            # crossing test
            if (ay > py) != (by > py) and px < (bx - ax) * (py - ay) / (by - ay) + ax:
                inside = not inside
        if inside:
            return 0.0
    return best


def fpid_of(owner) -> str:
    """Footprint library id, or the board-level bucket."""
    return (owner.GetFPIDAsString() if hasattr(owner, "GetFPIDAsString")
            else "<board-level>")


def min_distance(g, shape, rings_list) -> float:
    """Smallest centreline-to-pad-polygon distance over a whole shape, in nm.

    Walked at the same STEP_NM as the trimmer so the two agree about what is
    inside a keepout. This answers "does it violate?" separately from "where
    does it violate?", which is what lets a compliant shape be left untouched.
    """
    if shape == "Line":
        s, e = g.GetStart(), g.GetEnd()
        length = math.hypot(e.x - s.x, e.y - s.y)
        n = max(2, int(length / STEP_NM) + 1)
        pts = [(s.x + (e.x - s.x) * i / n, s.y + (e.y - s.y) * i / n)
               for i in range(n + 1)]
    else:
        c, r = g.GetCenter(), g.GetRadius()
        if shape == "Circle":
            a0, span = 0.0, 2.0 * math.pi
        else:
            s = g.GetStart()
            a0 = math.atan2(s.y - c.y, s.x - c.x)
            span = math.radians(g.GetArcAngle().AsDegrees())
        n = max(8, int(abs(span) * r / STEP_NM) + 1)
        pts = [(c.x + r * math.cos(a0 + span * i / n),
                c.y + r * math.sin(a0 + span * i / n)) for i in range(n + 1)]
    best = float("inf")
    for rings in rings_list:
        for px, py in pts:
            d = dist_point_poly(px, py, rings)
            if d < best:
                best = d
                if best == 0.0:
                    return 0.0
    return best


def blocked_at(t: float, sx, sy, ex, ey, keepouts) -> bool:
    px, py = sx + (ex - sx) * t, sy + (ey - sy) * t
    for rings, limit in keepouts:
        if dist_point_poly(px, py, rings) < limit:
            return True
    return False


def clear_intervals(sx, sy, ex, ey, keepouts):
    """Sub-intervals of the segment that clear every keepout."""
    length = math.hypot(ex - sx, ey - sy)
    if length == 0:
        return [(0.0, 1.0)] if not blocked_at(0.0, sx, sy, ex, ey, keepouts) else []
    steps = max(2, int(length / STEP_NM) + 1)
    flags = [blocked_at(i / steps, sx, sy, ex, ey, keepouts) for i in range(steps + 1)]

    def refine(lo, hi):                     # lo/hi are t with differing flags
        want = flags_at_lo = blocked_at(lo, sx, sy, ex, ey, keepouts)
        while (hi - lo) * length > REFINE_NM:
            mid = (lo + hi) / 2
            if blocked_at(mid, sx, sy, ex, ey, keepouts) == want:
                lo = mid
            else:
                hi = mid
        return hi if flags_at_lo else lo

    spans, start = [], None
    for i in range(steps + 1):
        t = i / steps
        if not flags[i] and start is None:
            start = refine((i - 1) / steps, t) if i else 0.0
        elif flags[i] and start is not None:
            spans.append((start, refine((i - 1) / steps, t)))
            start = None
    if start is not None:
        spans.append((start, 1.0))
    return [(a, b) for a, b in spans if (b - a) * length >= MIN_KEEP_NM]


def clear_arcs(cx, cy, radius, a0, a1, keepouts):
    """Angular sub-intervals of an arc/circle that clear every keepout.

    Same walk-and-bisect as clear_intervals, in angle instead of along a
    parameter. a0..a1 are radians and may wrap; a full circle passes
    a1 = a0 + 2*pi. Returns [(start_rad, end_rad), ...] in the same sweep
    direction, dropping survivors whose ARC LENGTH is below MIN_KEEP_NM --
    a 0.1 mm stub of a circle is ink noise exactly as a short line is.
    """
    span = a1 - a0
    arclen = abs(span) * radius
    if arclen <= 0:
        return []

    def blocked(u):                       # u in 0..1 along the sweep
        th = a0 + span * u
        px, py = cx + radius * math.cos(th), cy + radius * math.sin(th)
        for rings, limit in keepouts:
            if dist_point_poly(px, py, rings) < limit:
                return True
        return False

    steps = max(8, int(arclen / STEP_NM) + 1)
    flags = [blocked(i / steps) for i in range(steps + 1)]

    def refine(lo, hi):
        want = blocked(lo)
        while (hi - lo) * arclen > REFINE_NM:
            mid = (lo + hi) / 2
            if blocked(mid) == want:
                lo = mid
            else:
                hi = mid
        return hi if want else lo

    spans, start = [], None
    for i in range(steps + 1):
        u = i / steps
        if not flags[i] and start is None:
            start = refine((i - 1) / steps, u) if i else 0.0
        elif flags[i] and start is not None:
            spans.append((start, refine((i - 1) / steps, u)))
            start = None
    if start is not None:
        spans.append((start, 1.0))
    return [(a0 + span * a, a0 + span * b) for a, b in spans
            if (b - a) * arclen >= MIN_KEEP_NM]


def main() -> int:
    ap = argparse.ArgumentParser(description=__doc__.splitlines()[0])
    ap.add_argument("board")
    ap.add_argument("--apply", action="store_true", help="write the board")
    ap.add_argument("--clearance", type=float, default=CLEARANCE_MM)
    ap.add_argument("--margin", type=float, default=MARGIN_MM,
                    help="extra cut to absorb pad-polygon approximation error")
    ap.add_argument("--min-width", type=float, default=MIN_SILK_WIDTH_MM,
                    help="floor for narrowing: the thinnest line the fab will "
                         "print. Below this a shape must be trimmed instead.")
    ap.add_argument("--neighbour-refs", default="",
                    help="comma-separated references that ALSO trim against "
                         "other parts' pads. Only safe where divergence cannot "
                         "result -- a type with a single placement has nothing "
                         "to diverge from. Naming them here keeps the decision "
                         "in the command rather than inferred from a count.")
    ap.add_argument("--scope", choices=("own", "all"), default="own",
                    help="'own' (default) trims a footprint's silk against its "
                         "own pads only, which keeps every placement of a type "
                         "identical and therefore mirrorable into the library. "
                         "'all' trims against every nearby pad -- correct for "
                         "this board, divergent across instances, library-hostile.")
    args = ap.parse_args()

    neighbour_refs = {r.strip() for r in args.neighbour_refs.split(",") if r.strip()}

    board = pcbnew.LoadBoard(args.board)
    silk_layers = (pcbnew.F_SilkS, pcbnew.B_SilkS)
    mask_of = {pcbnew.F_SilkS: pcbnew.F_Mask, pcbnew.B_SilkS: pcbnew.B_Mask}

    pads_by_mask = {m: [] for m in mask_of.values()}
    own_pads: dict = {}          # footprint uuid -> {mask layer: [pad, ...]}
    for fp in board.GetFootprints():
        slot = own_pads.setdefault(str(fp.m_Uuid.AsString()),
                                   {m: [] for m in mask_of.values()})
        for pad in fp.Pads():
            for m in pads_by_mask:
                if pad.IsOnLayer(m):
                    pads_by_mask[m].append(pad)
                    slot[m].append(pad)
    poly_cache = {}

    trimmed = deleted = kept = narrowed = 0
    deferred = collections.Counter()
    per_fp = collections.Counter()
    removed_fp = collections.Counter()
    narrow_fp = collections.Counter()
    total_fp = collections.Counter()
    edits = []

    # Footprint graphics, then board-level ones. Board drawings belong to no
    # footprint, so there is no library half to mirror -- they are edited here
    # or not at all.
    owners = [(fp, list(fp.GraphicalItems())) for fp in board.GetFootprints()]
    owners.append((board, [d for d in board.GetDrawings()
                           if d.GetLayer() in silk_layers]))

    for fp, items in owners:
        for g in items:
            lay = g.GetLayer()
            if lay not in silk_layers or g.GetClass() != "PCB_SHAPE":
                continue
            total_fp[fpid_of(fp)] += 1
            shape = g.ShowShape()
            if shape not in ("Line", "Circle", "Arc"):
                # A Polygon on silk is usually a polarity band or a pin-1 dot;
                # cutting it destroys the meaning the marker exists to carry.
                deferred[shape] += 1
                continue
            half = g.GetWidth() / 2.0
            limit = (args.clearance + args.margin) * NM + half
            mask_layer = mask_of[lay]

            if shape == "Line":
                s, e = g.GetStart(), g.GetEnd()
                box = (min(s.x, e.x), min(s.y, e.y), max(s.x, e.x), max(s.y, e.y))
            else:
                c, r = g.GetCenter(), g.GetRadius()
                box = (c.x - r, c.y - r, c.x + r, c.y + r)

            # Board-level drawings (fp is the BOARD) have no library definition
            # to diverge from, so they always see every pad. A footprint's silk
            # sees only its own pads under the default scope -- see the module
            # docstring for why that is the mirrorable choice.
            if (args.scope == "own" and fp is not board
                    and fp.GetReference() not in neighbour_refs):
                candidates = own_pads[str(fp.m_Uuid.AsString())][mask_layer]
            else:
                candidates = pads_by_mask[mask_layer]

            near = []
            for pad in candidates:
                key = (id(pad), mask_layer)
                if key not in poly_cache:
                    poly_cache[key] = poly_points(pad, mask_layer)
                rings = poly_cache[key]
                if not rings:
                    continue
                bb = pad.GetBoundingBox()
                if box[2] < bb.GetLeft() - limit or box[0] > bb.GetRight() + limit:
                    continue
                if box[3] < bb.GetTop() - limit or box[1] > bb.GetBottom() + limit:
                    continue
                near.append(rings)
            if not near:
                continue

            # Does it violate the REQUIREMENT, or only the requirement plus the
            # margin? Cutting everything inside clearance+margin treats a
            # compliant shape as a defect: on Board3 that deleted 137 shapes
            # sitting in the 0.150-0.170 band, all 62 R0603 outlines among them
            # (min gap 0.1522 mm -- above the limit, below limit+margin). The
            # margin is there to stop the inscribed-polygon error deciding a
            # borderline cut, not to widen the requirement.
            d_min = min_distance(g, shape, near)
            if (d_min - half) / NM >= args.clearance:
                continue

            # Clearance is edge-to-edge on a stored centreline, so narrowing a
            # line buys clearance with NO geometry change. Prefer it: it keeps
            # the marking whole and legible where trimming would break or
            # delete it. Bounded below by what the fab can print, so this is
            # only available when the centreline has room for both.
            max_w = 2.0 * (d_min / NM - args.clearance)
            if max_w >= args.min_width and g.GetWidth() > args.min_width * NM:
                new_w = max(args.min_width, min(g.GetWidth() / NM, max_w) - args.margin)
                if new_w >= args.min_width:
                    narrowed += 1
                    narrow_fp[fpid_of(fp)] += 1
                    edits.append(("width", fp, g, int(round(new_w * NM)), None, None))
                    continue

            keep = [(rings, limit) for rings in near]

            if shape == "Line":
                s, e = g.GetStart(), g.GetEnd()
                spans = clear_intervals(s.x, s.y, e.x, e.y, keep)
                if len(spans) == 1 and spans[0] == (0.0, 1.0):
                    continue
                edits.append(("line", fp, g, spans, s, e))
            else:
                c, r = g.GetCenter(), g.GetRadius()
                if shape == "Circle":
                    a0, a1 = 0.0, 2.0 * math.pi
                else:
                    s, e = g.GetStart(), g.GetEnd()
                    a0 = math.atan2(s.y - c.y, s.x - c.x)
                    a1 = a0 + math.radians(g.GetArcAngle().AsDegrees())
                spans = clear_arcs(c.x, c.y, r, a0, a1, keep)
                if len(spans) == 1 and abs((spans[0][1] - spans[0][0]) - (a1 - a0)) < 1e-9:
                    continue
                edits.append(("arc", fp, g, spans, (c, r), None))
            fpid = fpid_of(fp)
            if not spans:
                deleted += 1
                per_fp[fpid] += 0          # ensure the type appears
                removed_fp[fpid] += 1
            else:
                trimmed += 1
                kept += len(spans)
                per_fp[fpid] += 1

    print(f"board            : {args.board.split('/')[-1]}")
    print(f"scope            : {args.scope} pads   "
          f"(clearance {args.clearance} mm, margin {args.margin} mm)")
    print(f"shapes narrowed  : {narrowed}   (>= {args.min_width} mm, geometry unchanged)")
    print(f"shapes trimmed   : {trimmed}   (into {kept} pieces)")
    print(f"shapes removed   : {deleted}   (no clear span >= {MIN_KEEP_NM/NM} mm)")
    print(f"deferred shapes  : {dict(deferred)}   (polarity/pin-1 markers, left alone)")
    # Removed-vs-trimmed is the number that needs a human. A type whose silk is
    # entirely removed has had a design decision made for it by a threshold --
    # plausible for a chip passive, wrong for a connector an assembler orients
    # by -- so it must be visible here rather than inferred from a total.
    print("\nby footprint type   (narrowed / trimmed / REMOVED / total on the type)")
    for fpid in sorted(set(per_fp) | set(removed_fp) | set(narrow_fp),
                       key=lambda k: -(per_fp[k] + removed_fp[k] + narrow_fp[k])):
        tot = total_fp[fpid]
        rem = removed_fp[fpid]
        flag = "   <-- ALL SILK GONE" if rem and rem == tot else ""
        print(f"  {narrow_fp[fpid]:4d} / {per_fp[fpid]:4d} / {rem:4d} / {tot:4d}  {fpid}{flag}")

    if not args.apply:
        print("\n(report only -- pass --apply to write)")
        return 0

    for kind, fp, g, spans, a_data, b_data in edits:
        if kind == "width":
            # spans carries the new width in nm for this edit kind. Nothing
            # moves, so there is no piece to add and nothing to remove.
            g.SetWidth(spans)
            continue
        if kind == "line":
            s, e = a_data, b_data
            for a, b in spans:
                new = g.Duplicate()
                new.SetStart(pcbnew.VECTOR2I(int(s.x + (e.x - s.x) * a),
                                             int(s.y + (e.y - s.y) * a)))
                new.SetEnd(pcbnew.VECTOR2I(int(s.x + (e.x - s.x) * b),
                                           int(s.y + (e.y - s.y) * b)))
                fp.Add(new)
        else:
            c, r = a_data
            for a0, a1 in spans:
                new = g.Duplicate()
                new.SetShape(pcbnew.SHAPE_T_ARC)
                mid = (a0 + a1) / 2.0
                pt = lambda th: pcbnew.VECTOR2I(int(round(c.x + r * math.cos(th))),
                                                int(round(c.y + r * math.sin(th))))
                new.SetArcGeometry(pt(a0), pt(mid), pt(a1))
                fp.Add(new)
        fp.Remove(g)
        _KEEPALIVE.append(g)

    board.Save(args.board)
    print(f"\nwritten: {args.board}")
    return 0


if __name__ == "__main__":
    sys.exit(main())
