kms254/Mustang-Dash-Test/tools/kicad_handroute.py

#!/usr/bin/env python3
"""Apply a declarative copper edit to a .kicad_pcb, then refill zones correctly.

KTD5 says the flagged signal-integrity nets are hand-routed, never autorouted.
This is what "by hand" means here: the route is written down as coordinates,
reviewed as text, applied atomically, and measured afterwards with
tools/kicad_measure.py. Nothing is dragged in the editor, so nothing is
unreproducible.

  python tools/kicad_handroute.py board.kicad_pcb edit.json [--dry-run]

An edit is a single spec, or {"steps": [spec, spec, ...]} applied in order:

  {
    "move_footprints": [{"ref": "X1", "by": [0.5, 0.0]},
                        {"ref": "R33", "to": [136.0, 101.25], "rot": 180}],
    "delete":   [{"net": "CAN1_H", "bbox": [x1,y1,x2,y2], "layers": ["Bottom Layer"],
                  "vias": true}],
    "renet":    [{"from": "SCLK_L_MCU", "to": "SCLK_L", "bbox": [x1,y1,x2,y2],
                  "layers": ["Inner2"], "vias": true}],
    "add":      [{"net": "CAN1_H", "layer": "Top Layer", "width": 0.254,
                  "points": [[x,y], [x,y], ...]}],
    "add_vias": [{"net": "USB_DM_CONN", "at": [x,y], "diameter": 0.6, "drill": 0.3}],
    "move_fp_text": [{"ref": "R10", "field": "reference", "to": [x,y]}],
    "place_parts": [{"ref": "C72", "fpid": "lib:C0603", "libpath": "…/lib.pretty",
                     "value": "100nF", "at": [x,y], "rot": 90,
                     "nets": {"1": "+3V3", "2": "GND"}}],   # a part WITH a symbol
    "add_footprints": [{"ref": "FID1", "lib": "…", "name": "…", "at": [x,y]}],  # board-only
    "untent_vias": [{"at": [x,y], "net": "SCLK_C", "label": "TP1"}],
    "add_silk":  [{"text": "TT1", "at": [x,y], "height": 1.0, "thickness": 0.15}],
    "replace_footprints": [{"ref": "SW1", "fpid": "lib:FOOTPRINT",
                            "libpath": "kicad/board3/lib.pretty"}],
    "add_keepouts": [{"ref": "H2", "at": [x,y], "radius": 0.85,
                      "layers": ["F.Cu","In1.Cu","In2.Cu","B.Cu"]}]
  }

Deletion semantics: a track is removed only when BOTH endpoints are inside bbox,
a via when its centre is. A segment that merely passes through survives --
deleting those silently orphans copper outside the region you meant to touch.
Omit "bbox" to match a whole net, "layers" to match any layer. "renet" selects
by the same rule, and exists because moving a series element to the other end of
a run renames most of that run rather than re-laying it: re-adding copper rounds
every endpoint through millimetres, so geometry that was DRC-clean moves. Renet
keeps the integer nanometres and changes only the net.

"move_footprints" takes "by" (relative) or "to" (absolute), plus an optional
"rot" in degrees. Placing a two-pad part in series ON its own escape needs the
part aligned with the trace, so orientation is part of the placement, not a
separate GUI step.

Three traps this tool exists to absorb
--------------------------------------
1. THE REFILL MUST USE THE REAL RULES. Zone fills are clearance-dependent, and
   the tracked .kicad_pro still carries the importer's factory defaults
   (clearance 0.2 mm against the board's real 0.1016 -- see KTD2). Filling under
   those pulls every pour back an extra 0.1 mm, which moves thermal spokes and
   invents starved_thermal violations that look like your edit caused them. So
   the fill happens against a staged project carrying tools/kicad_rules.json,
   and the tracked project file is never written.

2. A THROUGH VIA IS CHECKED AGAINST ALL FOUR LAYERS. Board3 routes ~1600 mm of
   signal through Inner1 and Inner2, so "the top and bottom are clear here" says
   nothing about whether a via can land there. Check the inner layers before
   placing one: a via at (37.100,93.918) shorted an Inner1 VBUS run during U6.

3. board.GetTracks() RE-WRAPS THE LIVE CONTAINER. Call it again after a Remove()
   and you get a SwigPyObject that will not iterate. Snapshot once, up front.

4. A POUR FILLS TO min_clearance, BUT AN NPTH HOLE IS JUDGED BY min_hole_clearance.
   Board3 sets those to 0.1016 and 0.2, so every zone that reaches a mounting or
   alignment hole lands in the 0.084 mm gap between them and reports
   hole_clearance -- four layers x every hole, with nothing wrong upstream to fix.
   "add_keepouts" is the fix: a rule area over the hole that only bans the pour.
   It must NOT ban vias. The keepout belongs to the FOOTPRINT, so it travels with
   the part and the library copy stays the source of truth.
"""

from __future__ import annotations

import argparse
import json
import math
import os
import shutil
import subprocess
import sys
import tempfile
from pathlib import Path

HERE = Path(__file__).parent
RULES = HERE / "kicad_rules.json"
NM = 1_000_000

try:
    import pcbnew
except ImportError:  # depends on which interpreter invoked us
    # Re-run under KiCad's own interpreter, exactly once, so this works from any
    # shell -- same contract as tools/kicad_measure.py.
    if os.environ.get("KICAD_HANDROUTE_REEXEC"):
        raise SystemExit("pcbnew is not importable even under KiCad's interpreter.")
    sys.path.insert(0, str(HERE))
    from kicad_env import KiCadNotFound, find_kicad_python

    try:
        _interpreter = find_kicad_python()
    except KiCadNotFound as exc:
        raise SystemExit(str(exc))
    raise SystemExit(subprocess.run(
        [str(_interpreter), *sys.argv],
        env=dict(os.environ, KICAD_HANDROUTE_REEXEC="1")).returncode)


def to_nm(value: float) -> int:
    return int(round(value * NM))


def layer_id(board, name: str) -> int:
    for lid in board.GetEnabledLayers().CuStack():
        if name in (board.GetLayerName(lid), pcbnew.LayerName(lid)):
            return lid
    raise SystemExit(f"unknown copper layer: {name!r}")


# Removed board items must outlive SaveBoard. Letting a removed SWIG proxy be
# garbage-collected frees the underlying C++ object and corrupts the session --
# unrelated proxies turn into raw SwigPyObjects. apply_step's locals die before
# main() saves, so this deliberately leaks at module scope for the process
# lifetime. The "memory leak ... no destructor" warnings are this working.
_KEEPALIVE: list = []


def any_layer_id(board, name: str) -> int:
    """Resolve ANY layer by name, not just copper.

    layer_id() walks CuStack(), which is right for tracks and vias and useless
    for silkscreen. Board3 renames its layers ("Top Silkscreen Layer", not
    "F.SilkS"), so both the board's own name and KiCad's canonical name are
    accepted -- and layers are always compared by ID afterwards, never by name.
    """
    for lid in board.GetEnabledLayers().Seq():
        if name in (board.GetLayerName(lid), pcbnew.LayerName(lid)):
            return lid
    raise SystemExit(f"unknown layer: {name!r}")


def apply_step(board, spec: dict, tracks: list, dry: bool):
    netmap = {net.GetNetname().lstrip("/"): net
              for net in board.GetNetsByNetcode().values()}
    removed = added = 0

    for rule in spec.get("delete", []):
        net = rule["net"].lstrip("/")
        bbox = rule.get("bbox")
        layers = rule.get("layers")
        for track in tracks:
            if track.GetNetname().lstrip("/") != net:
                continue
            is_via = track.Type() == pcbnew.PCB_VIA_T
            if is_via and not rule.get("vias", True):
                continue
            if layers and not is_via and board.GetLayerName(track.GetLayer()) not in layers:
                continue
            start, end = track.GetStart(), track.GetEnd()
            if bbox:
                x1, y1, x2, y2 = bbox

                def inside(point) -> bool:
                    return x1 <= point.x / NM <= x2 and y1 <= point.y / NM <= y2

                if not inside(start):
                    continue
                if not is_via and not inside(end):
                    continue
            kind = "via" if is_via else board.GetLayerName(track.GetLayer())
            print(f"  - {net:<13} {kind:<13} ({start.x/NM:8.3f},{start.y/NM:8.3f})->"
                  f"({end.x/NM:8.3f},{end.y/NM:8.3f})")
            if not dry:
                board.Remove(track)
            removed += 1

    for rule in spec.get("renet", []):
        # Reassign copper from one net to another WITHOUT re-laying it. Splitting a
        # series element off the far end of a run means most of that run simply
        # changes name; deleting and re-adding it would round every endpoint
        # through millimetres and move geometry that is already DRC-clean.
        # Selection semantics are the same as "delete": both endpoints inside bbox.
        src = rule["from"].lstrip("/")
        dst = netmap[rule["to"].lstrip("/")]
        bbox = rule.get("bbox")
        layers = rule.get("layers")
        for track in tracks:
            if track.GetNetname().lstrip("/") != src:
                continue
            is_via = track.Type() == pcbnew.PCB_VIA_T
            if is_via and not rule.get("vias", True):
                continue
            if layers and not is_via and board.GetLayerName(track.GetLayer()) not in layers:
                continue
            start, end = track.GetStart(), track.GetEnd()
            if bbox:
                x1, y1, x2, y2 = bbox

                def inside(point) -> bool:
                    return x1 <= point.x / NM <= x2 and y1 <= point.y / NM <= y2

                if not inside(start):
                    continue
                if not is_via and not inside(end):
                    continue
            kind = "via" if is_via else board.GetLayerName(track.GetLayer())
            print(f"  > {src} -> {rule['to'].lstrip('/'):<13} {kind:<13} "
                  f"({start.x/NM:8.3f},{start.y/NM:8.3f})->"
                  f"({end.x/NM:8.3f},{end.y/NM:8.3f})")
            if not dry:
                track.SetNet(dst)

    for rule in spec.get("move_silk", []):
        # Move a BOARD-level silk text (not a footprint field). Matched on its
        # exact string, with an optional "at" to disambiguate when the same
        # legend appears twice -- TERM1/TERM2 are distinct, but CAN1/CAN2 style
        # pairs are one edit away from being ambiguous, so the guard is cheap.
        want = rule["text"]
        near = rule.get("at")
        dx, dy = rule["by"]
        hits = []
        for d in board.GetDrawings():
            if not hasattr(d, "GetText") or d.GetText() != want:
                continue
            if near is not None:
                p = d.GetPosition()
                if abs(p.x - to_nm(near[0])) > to_nm(0.5) or \
                   abs(p.y - to_nm(near[1])) > to_nm(0.5):
                    continue
            hits.append(d)
        if len(hits) != 1:
            raise SystemExit(
                f"move_silk {want!r}: matched {len(hits)} items, expected exactly 1 "
                f"-- add or correct 'at' to disambiguate")
        pos = hits[0].GetPosition()
        moved = pcbnew.VECTOR2I(pos.x + to_nm(dx), pos.y + to_nm(dy))
        if not dry:
            hits[0].SetPosition(moved)
        print(f"  ~ silk {want!r} by ({dx},{dy}) -> "
              f"({moved.x/NM:.3f},{moved.y/NM:.3f})")

    for rule in spec.get("add_silk", []):
        # Board-level silkscreen text. Defaults match the 16 labels U45 placed
        # (1.0 mm high, 0.15 mm stroke) so the board reads as one hand -- and
        # 0.15 mm is also the process minimum, so do not go below it.
        text = pcbnew.PCB_TEXT(board)
        x, y = rule["at"]
        text.SetText(rule["text"])
        text.SetPosition(pcbnew.VECTOR2I(to_nm(x), to_nm(y)))
        text.SetLayer(any_layer_id(board, rule.get("layer", "Top Silkscreen Layer")))
        text.SetTextHeight(to_nm(rule.get("height", 1.0)))
        text.SetTextWidth(to_nm(rule.get("width", 1.0)))
        text.SetTextThickness(to_nm(rule.get("thickness", 0.15)))
        text.SetHorizJustify(pcbnew.GR_TEXT_H_ALIGN_CENTER)
        text.SetVertJustify(pcbnew.GR_TEXT_V_ALIGN_CENTER)
        if rule.get("angle"):
            text.SetTextAngleDegrees(rule["angle"])
        if rule.get("mirror"):
            text.SetMirrored(True)
        board.Add(text)
        print(f"  T {rule['text']:<10} {rule.get('layer','Top Silkscreen Layer'):<21} "
              f"({x:8.3f},{y:8.3f})")
        added += 1
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
